emard/ulx3s/doc/esp-wroom-32.jpg

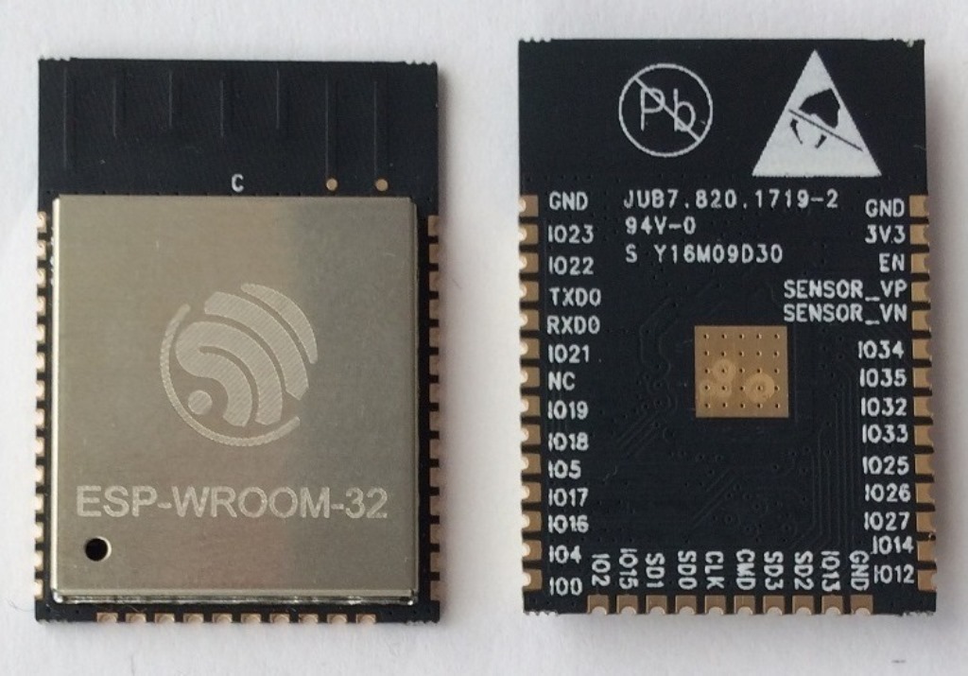
doc/esp-wroom-32.jpg
