emard/ulx3s/doc/oled-ssd1331.jpg

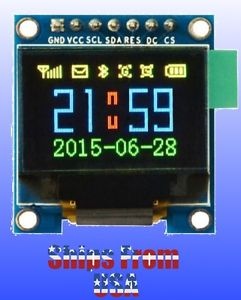
doc/oled-ssd1331.jpg
