emard/ulx3s/doc/sdcard/sdcard-schd3a010/ALPS-SCHD3A0100.GIF

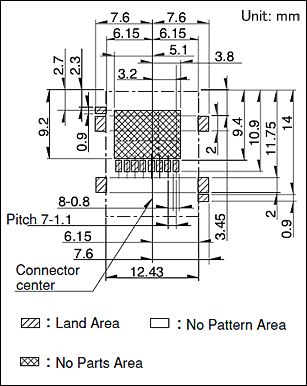
doc/sdcard/sdcard-schd3a010/ALPS-SCHD3A0100.GIF
