emard/ulx3s/pic/ulx3s-v316-bot.jpg

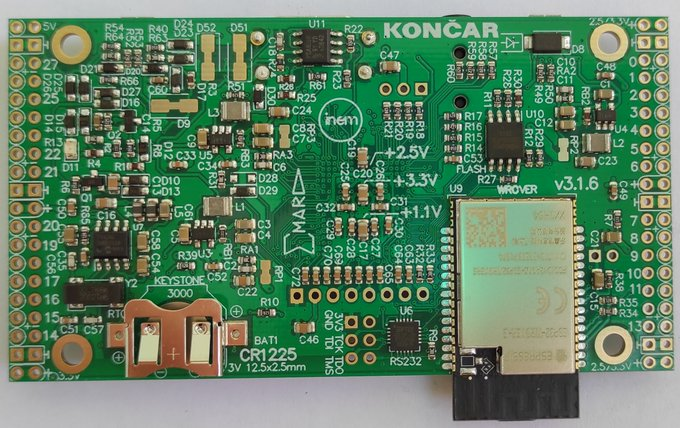
pic/ulx3s-v316-bot.jpg
