emard/ulx3s/pic/ulx3s-v316-top.jpg

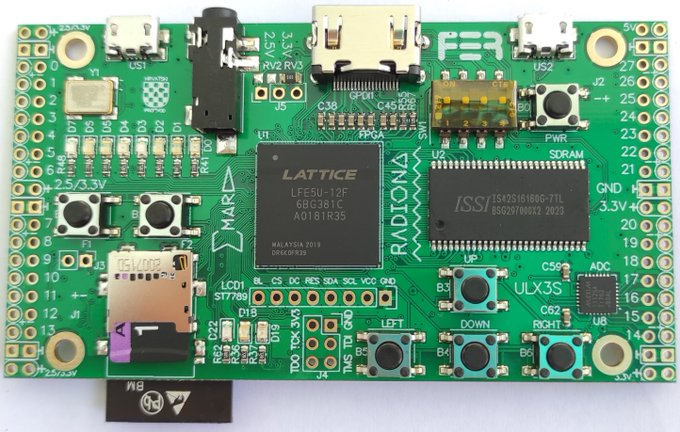
pic/ulx3s-v316-top.jpg
