emard/ulx3s/pic/ULX3S_v303_bottom.png

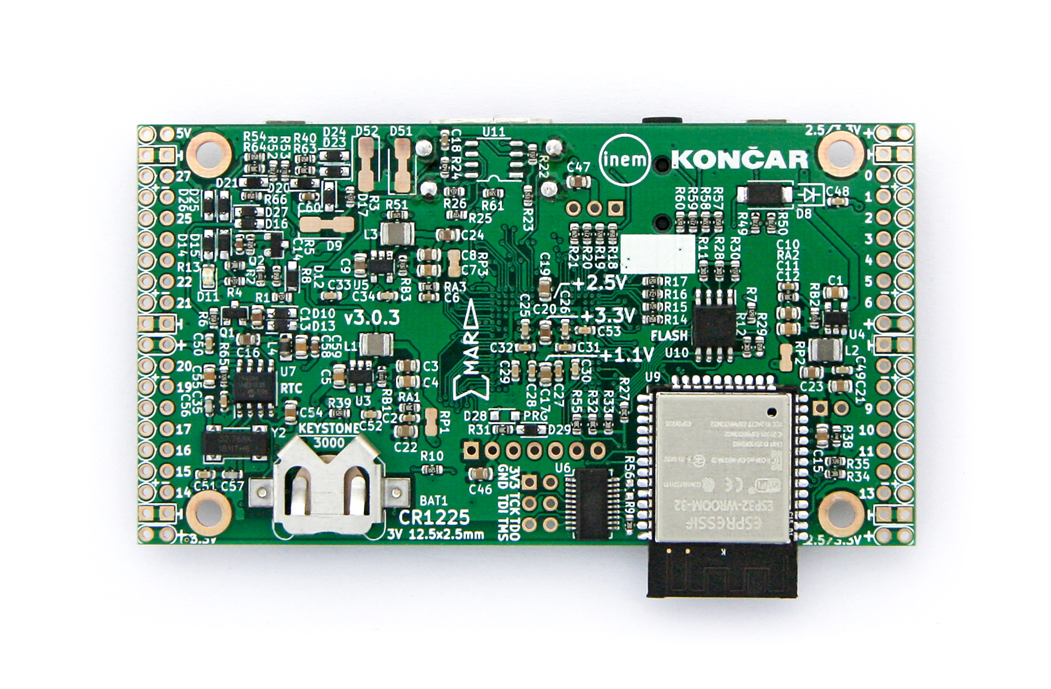
pic/ULX3S_v303_bottom.png
