emard/ulx3s/pic/ULX3S_v303_top.png

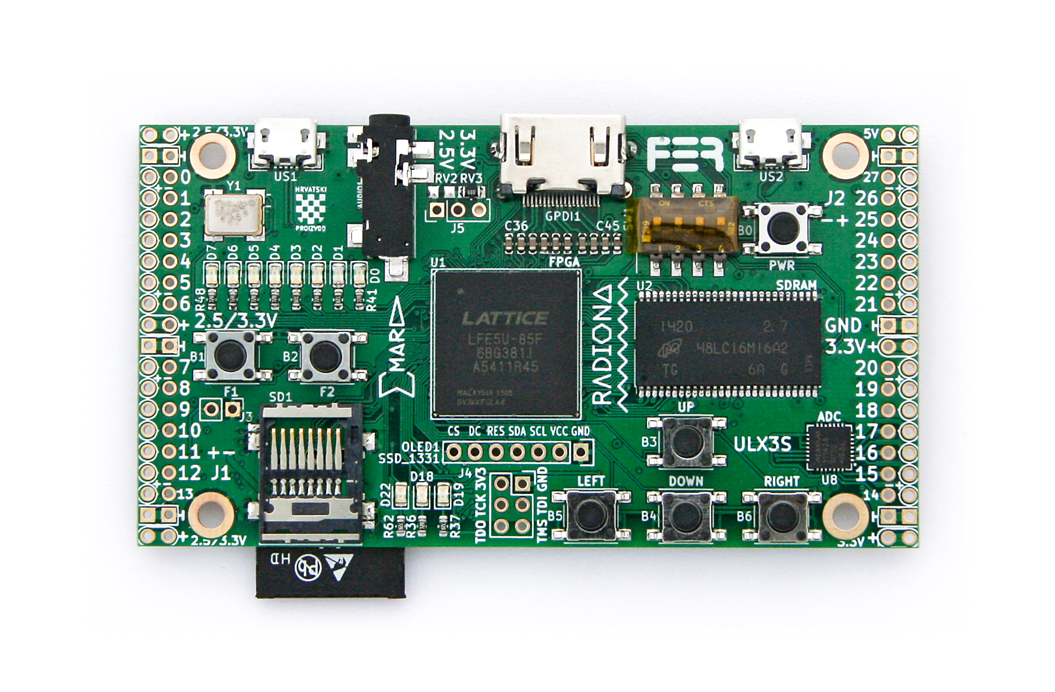
pic/ULX3S_v303_top.png
