emard/ulx3s/pic/ULX3S_v303_XRay1.jpg

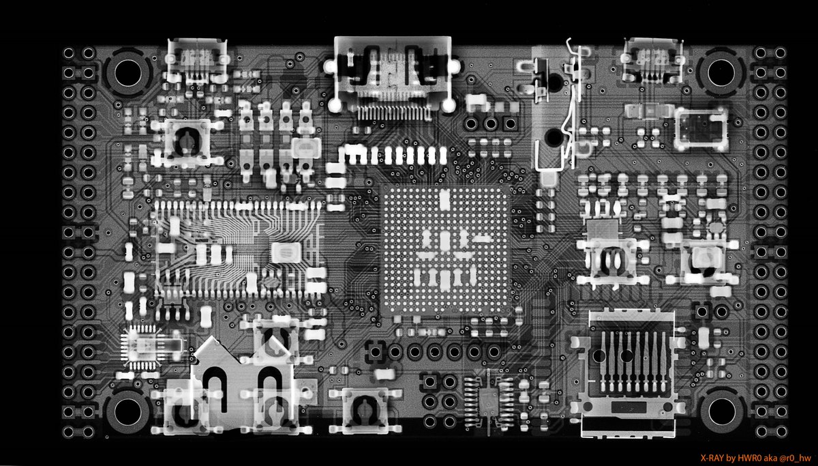
pic/ULX3S_v303_XRay1.jpg
