emard/ulx3s/pic/ULX3S_v303_XRay2.jpg

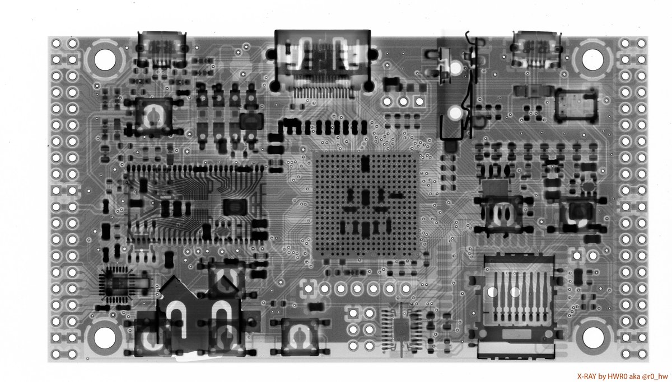
pic/ULX3S_v303_XRay2.jpg
