emard/ulx3s/pic/ULX3S_v303_XRay3.jpg

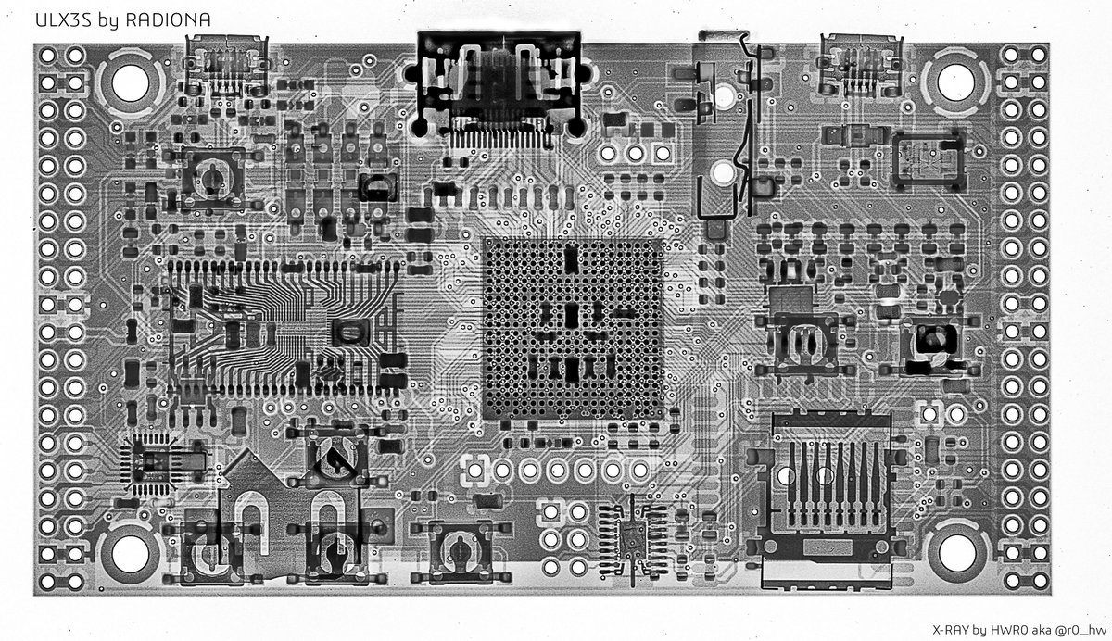
pic/ULX3S_v303_XRay3.jpg
