emard/ulx3s/pic/ULX3S_v307_IR_bottom.jpg

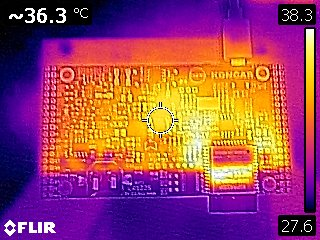
pic/ULX3S_v307_IR_bottom.jpg
