emard/ulx3s/pic/ulx3sb-v17.jpg

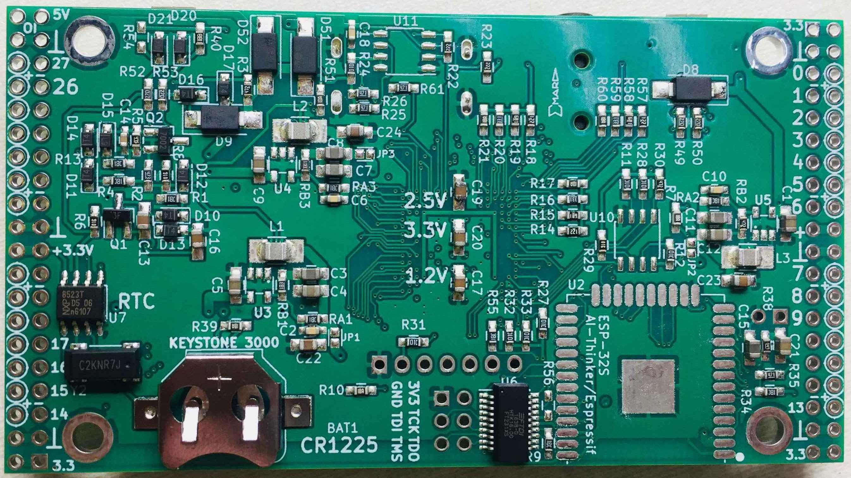
pic/ulx3sb-v17.jpg
