emard/ulx3s/pic/ulx3sb-v18-breakout-c19.png

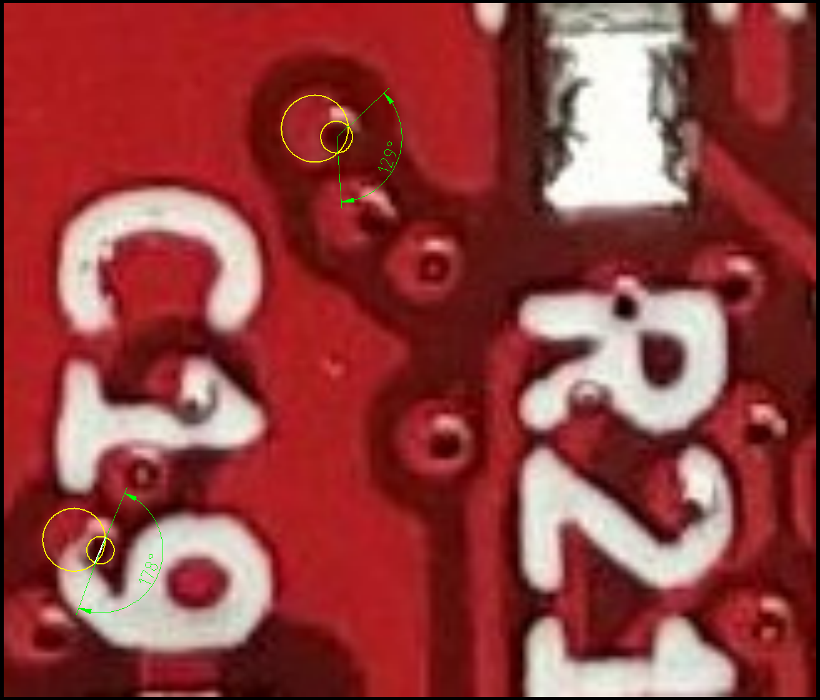
pic/ulx3sb-v18-breakout-c19.png
