emard/ulx3s/pic/ulx3sb-v18.jpg

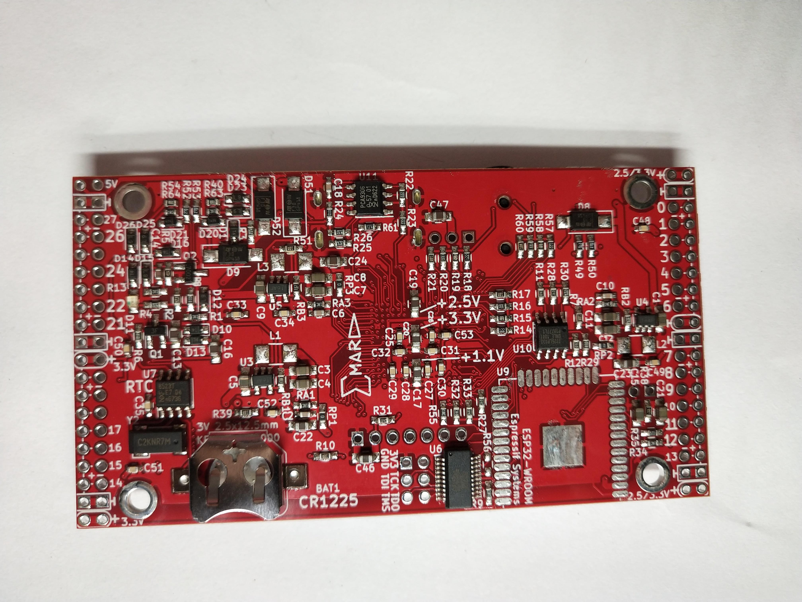
pic/ulx3sb-v18.jpg
