emard/ulx3s/pic/ulx3sb-v212.jpg

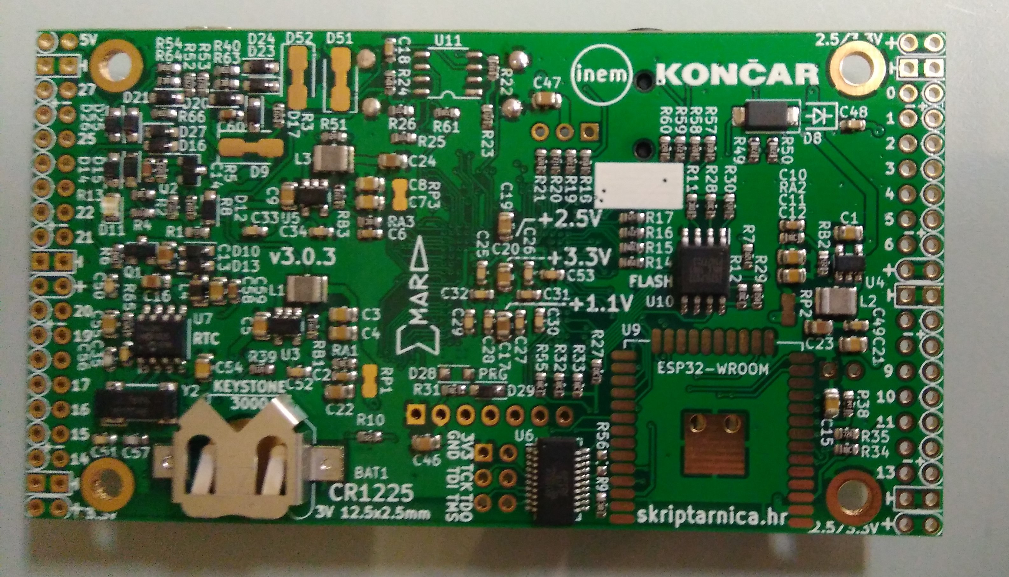
pic/ulx3sb-v212.jpg
