emard/ulx3s/pic/ulx3st-v17.jpg

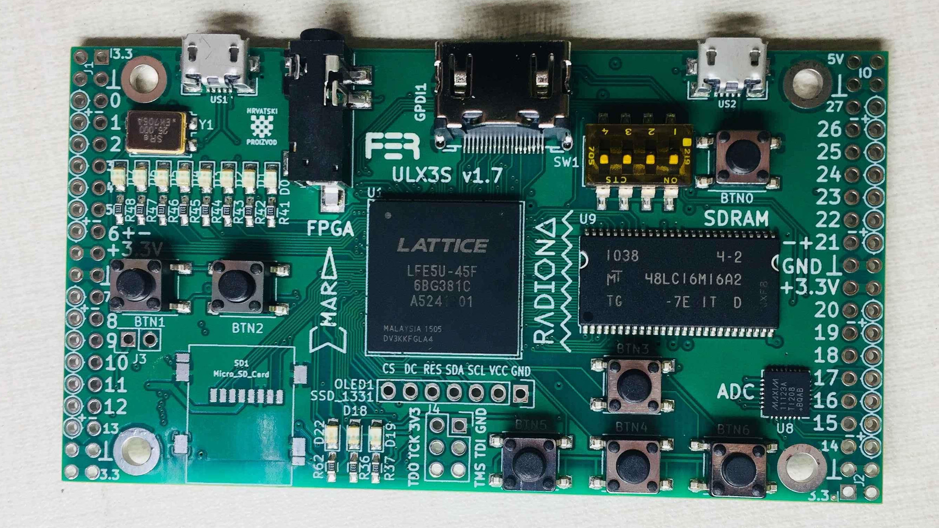
pic/ulx3st-v17.jpg
