emard/ulx3s/pic/ulx3st-v18.jpg

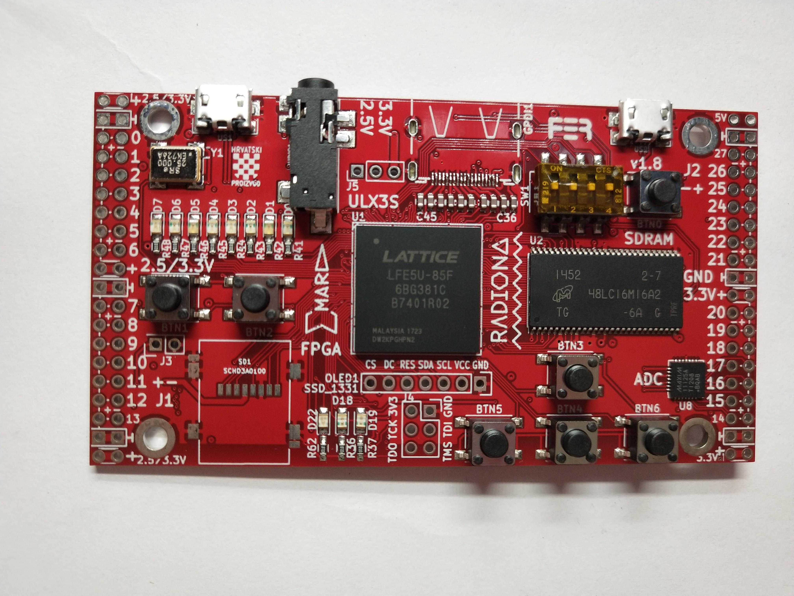
pic/ulx3st-v18.jpg
