emard/ulx3s/pic/ulx3st-v212.jpg

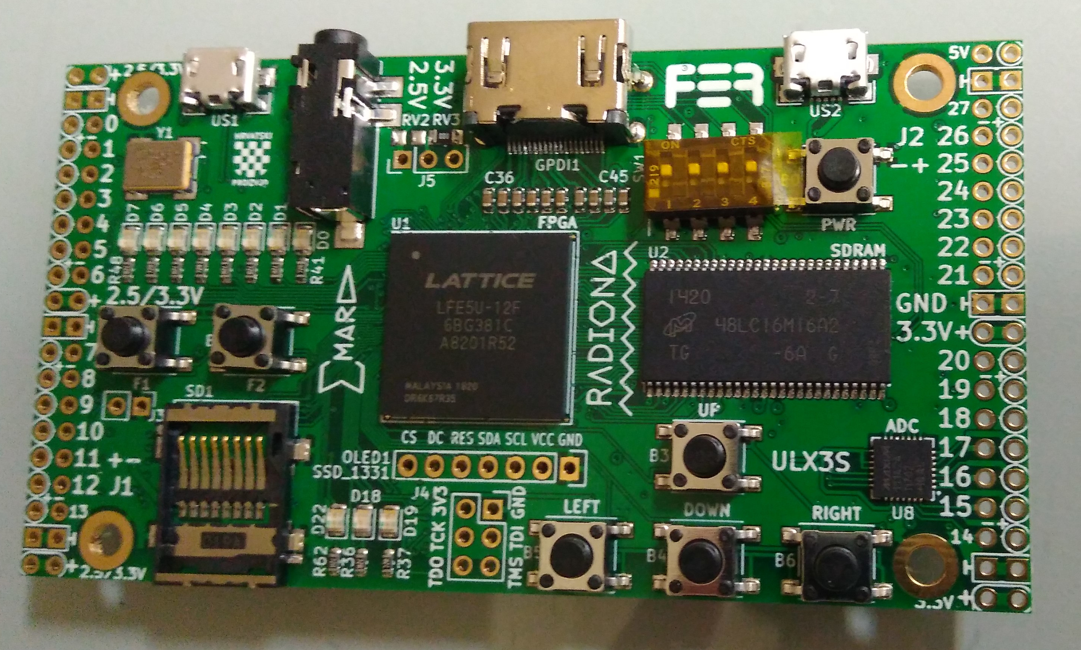
pic/ulx3st-v212.jpg
