emard/ulx3s/pic/ulx3st-v303.jpg

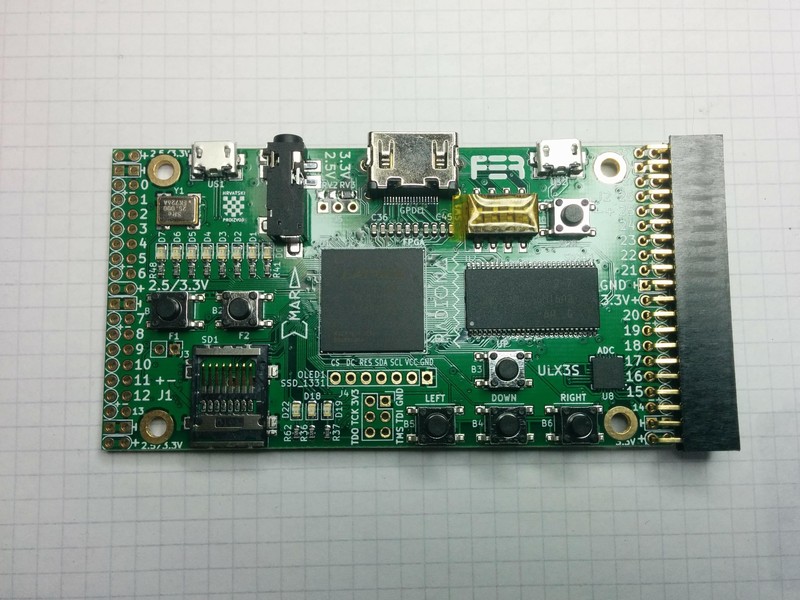
pic/ulx3st-v303.jpg
