emard/ulx3s/doc/schematics_v314.pdf

click on mouse pointer arrow on top of right toolbar
and double-click on sheet to open
Root sheet Sheet: power

Sheet: usb File: usb.sch

Sheet: serdes File: serdes.sch Sheet: flash File: flash.sch Sheet: analog

1 H4 HOLE GND GND GND GND

File: ram.sch Sheet: wifi File: wifi.sch Sheet: gpdi

File: ulx3s.sch Sheet: / EMARD

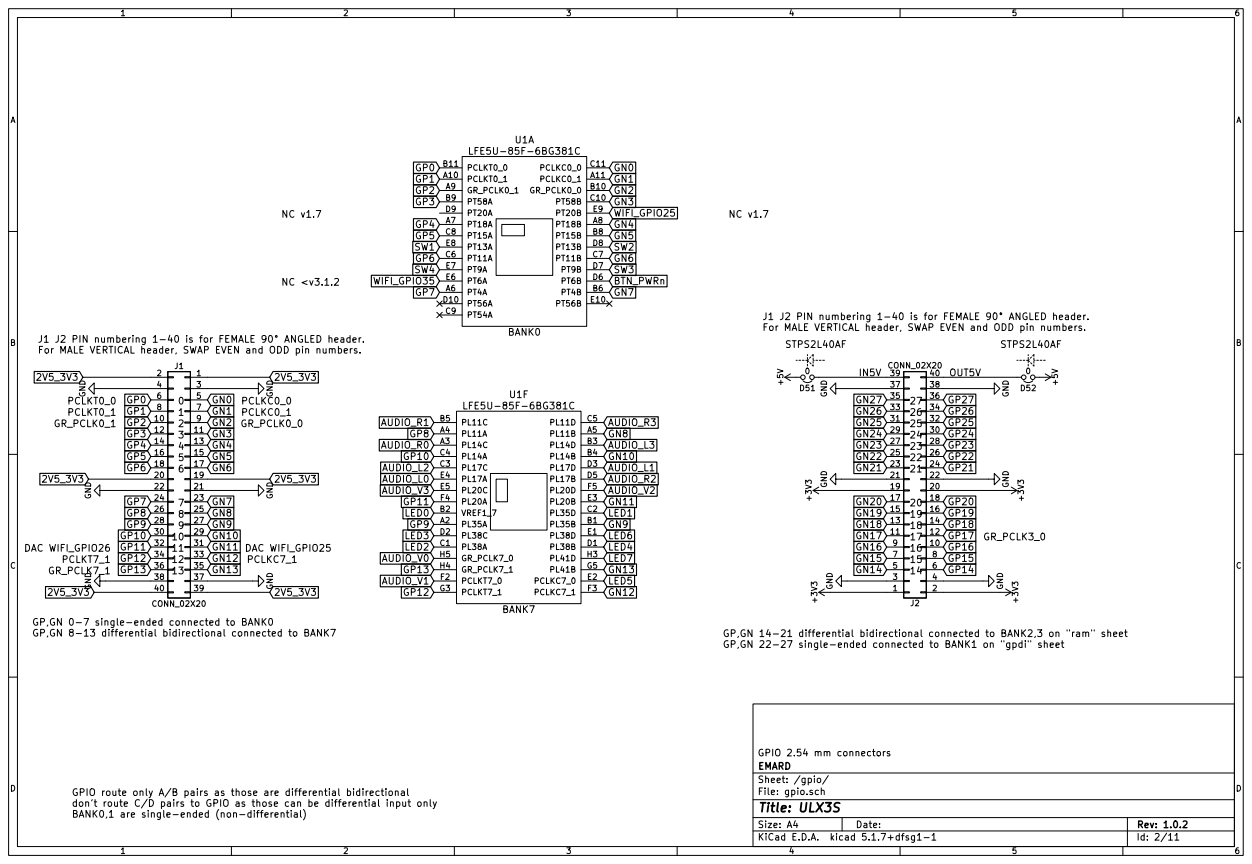
[picture p65: page 2]

J1 J2 PIN numbering 1-40 is for FEMALE 90° ANGLED header.
For MALE VERTICAL header, SWAP EVEN and ODD pin numbers.
STPS2L40AF

STPS2L40AF J1 J2 PIN numbering 1-40 is for FEMALE 90° ANGLED header.

GP,GN 0-7 single-ended connected to BANK0
GP,GN 8-13 differential bidirectional connected to BANK7

GP,GN 22-27 single-ended connected to BANK1 on "gpdi" sheet

GPIO route only A/B pairs as those are differential bidirectional
don't route C/D pairs to GPIO as those can be differential input only

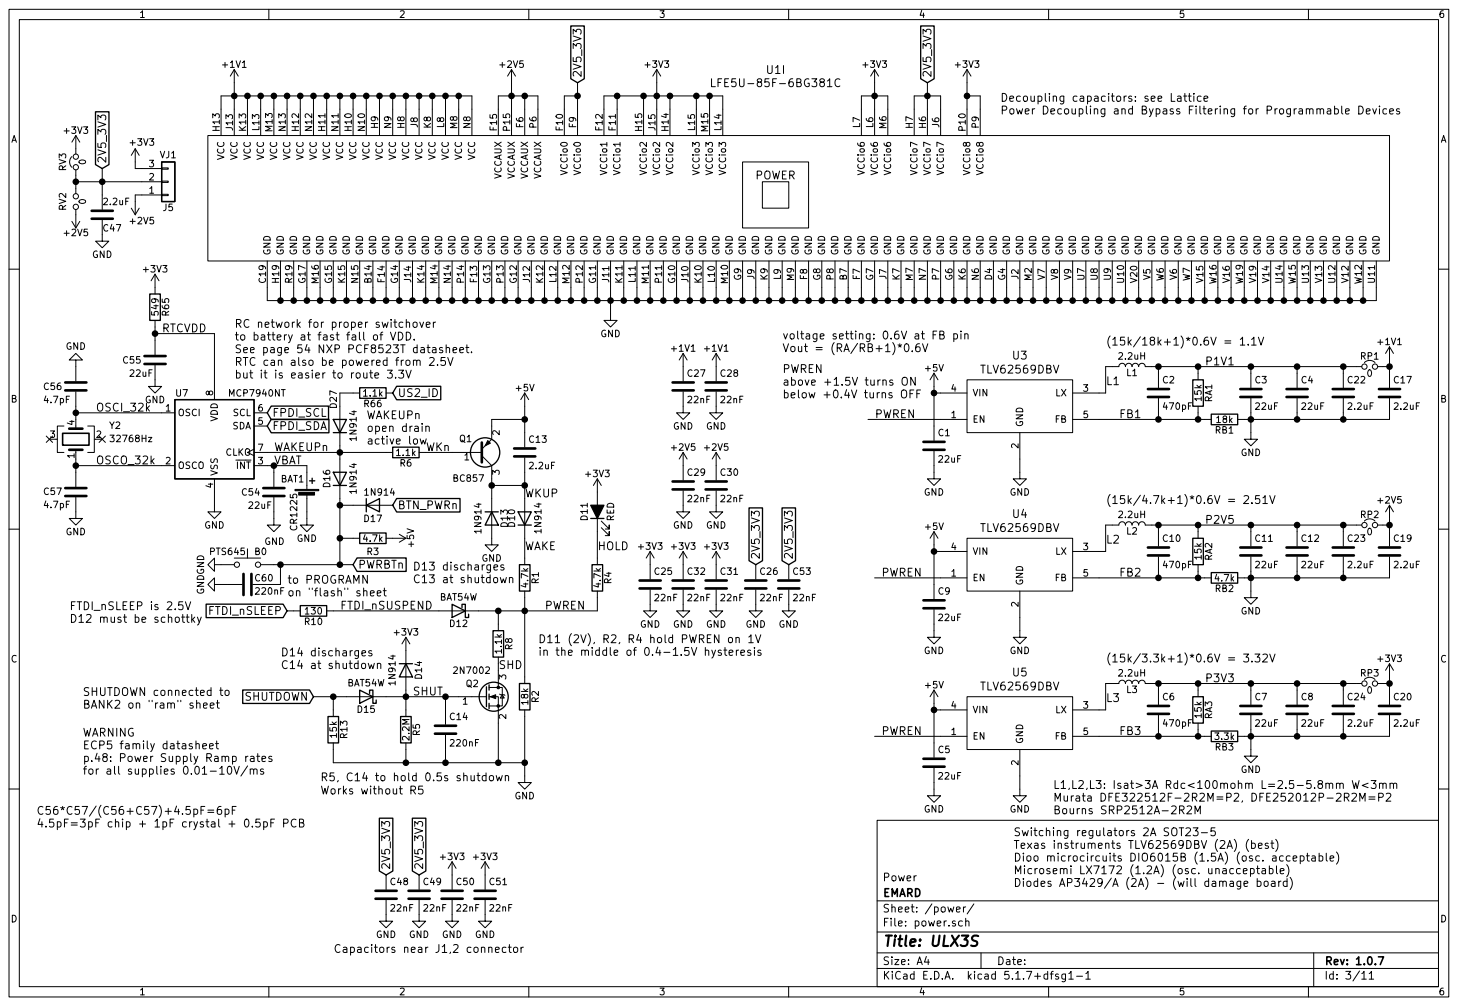
[picture p66: page 3]

RC network for proper switchover
to battery at fast fall of VDD.
See page 54 NXP PCF8523T datasheet.
RTC can also be powered from 2.5V

voltage setting: 0.6V at FB pin
Vout = (RA/RB+1)*0.6V
PWREN
above +1.5V turns ON
below +0.4V turns OFF

4 SDA 5 SCL 6 CLKO 7 VDD
18k BAT1CR1225 GND

open drain active low

D11 (2V), R2, R4 hold PWREN on 1V
in the middle of 0.4-1.5V hysteresis

WARNING
ECP5 family datasheet
p.48: Power Supply Ramp rates
for all supplies 0.01-10V/ms

Switching regulators 2A SOT23-5
Texas instruments TLV62569DBV (2A) (best)
Dioo microcircuits DIO6015B (1.5A) (osc. acceptable)
Microsemi LX7172 (1.2A) (osc. unacceptable)
Diodes AP3429/A (2A) - (will damage board)

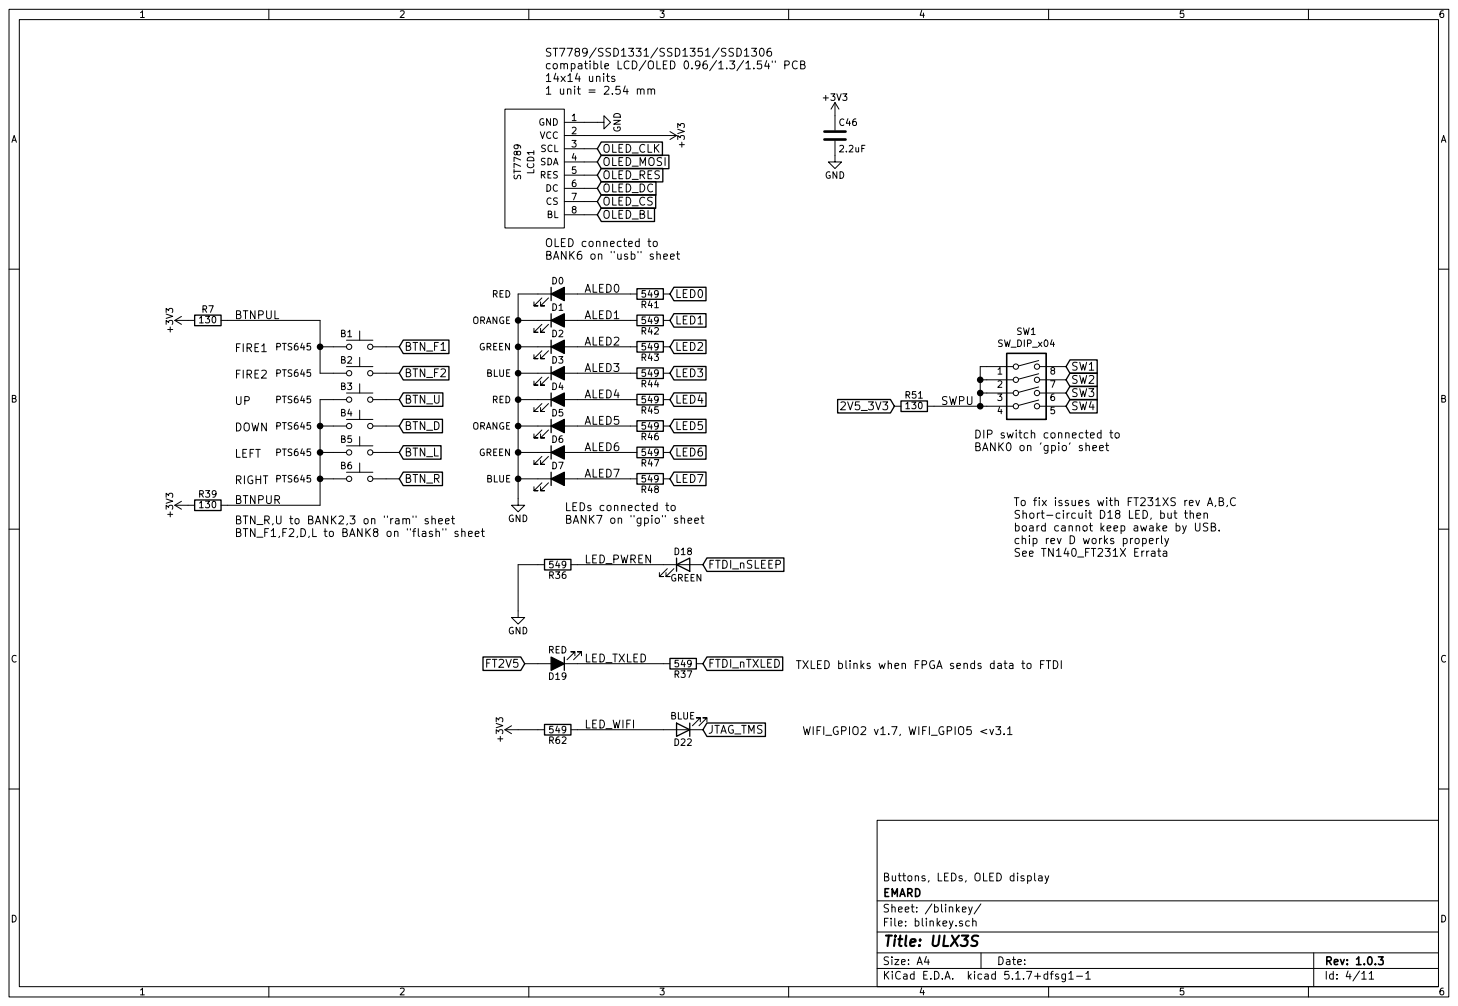
[picture p67: page 4]

ST7789/SSD1331/SSD1351/SSD1306
compatible LCD/OLED 0.96/1.3/1.54" PCB 14x14 units 1 unit = 2.54 mm
D2 GREEN
549 D6 GREEN

OLED connected to BANK6 on "usb" sheet BTN_R,U to BANK2,3 on "ram" sheet

BTN_F1,F2,D,L to BANK8 on "flash" sheet LEFT

LEDs connected to BANK7 on "gpio" sheet

To fix issues with FT231XS rev A,B,C
Short-circuit D18 LED, but then
board cannot keep awake by USB.
chip rev D works properly
See TN140_FT231X Errata

TXLED blinks when FPGA sends data to FTDI

Buttons, LEDs, OLED display
Sheet: /blinkey/ EMARD

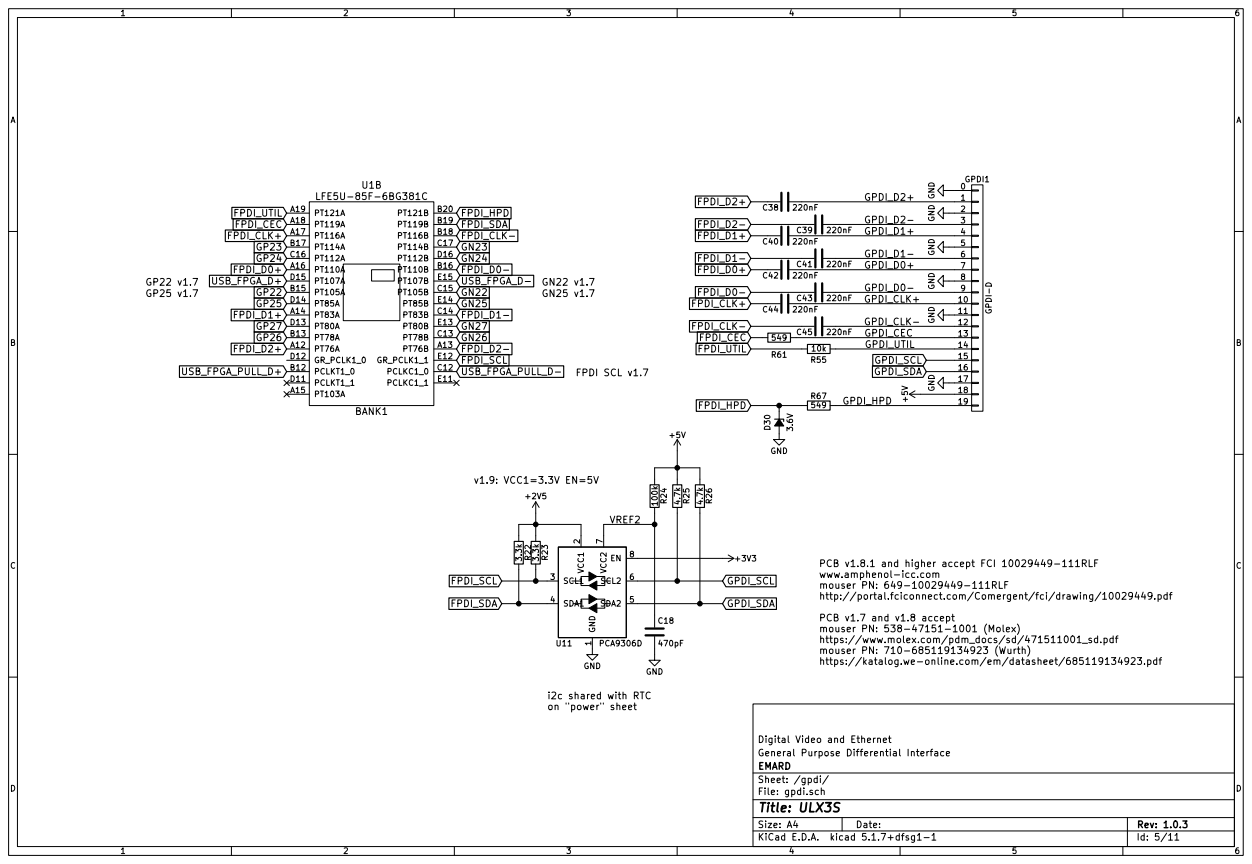
[picture p68: page 5]

FPDI_D2+
Digital Video and Ethernet R61

GPDI_D0+ | 7

GPDI_CLK+ | 10

13
14

PCB v1.8.1 and higher accept FCI 10029449-111RLF
www.amphenol-icc.com
mouser PN: 649-10029449-111RLF
http://portal.fciconnect.com/Comergent/fci/drawing/10029449.pdf

PCB v1.7 and v1.8 accept
mouser PN: 538-47151-1001 (Molex)
https://www.molex.com/pdm_docs/sd/471511001_sd.pdf
mouser PN: 710-685119134923 (Wurth)
https://katalog.we-online.com/em/datasheet/685119134923.pdf

Sheet: /gpdi/ EMARD General Purpose Differential Interface

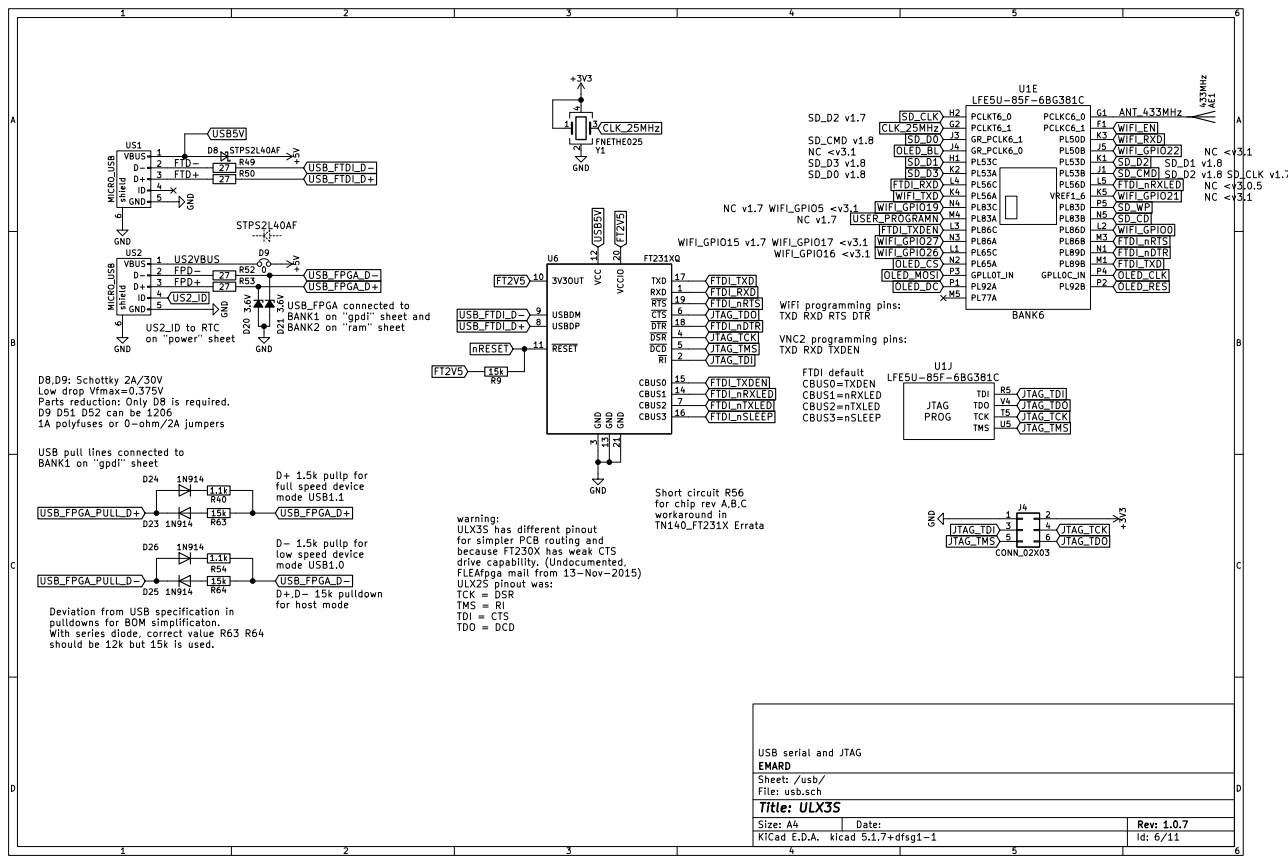
[picture p69: page 6]

3 DSR 4 DCD 5 CTS 6 CBUS2 7 USBDP 8 USBDM 9

WiFi programming pins:
TXD RXD RTS DTR

VNC2 programming pins: TXD RXD TXDEN

D8,D9: Schottky 2A/30V
Low drop Vfmax=0.375V
Parts reduction: Only D8 is required. D9 D51 D52 can be 1206

1A polyfuses or 0-ohm/2A jumpers

USB pull lines connected to
BANK1 on "gpdi" sheet

warning:
ULX3S has different pinout
for simpler PCB routing and
because FT230X has weak CTS
drive capability. (Undocumented,
FLEAfpga mail from 13-Nov-2015)
ULX2S pinout was:
TCK = DSR
TMS = RI
TDI = CTS
TDO = DCD

Deviation from USB specification in
pulldowns for BOM simplificaton.

File: usb.sch Sheet: /usb/ EMARD

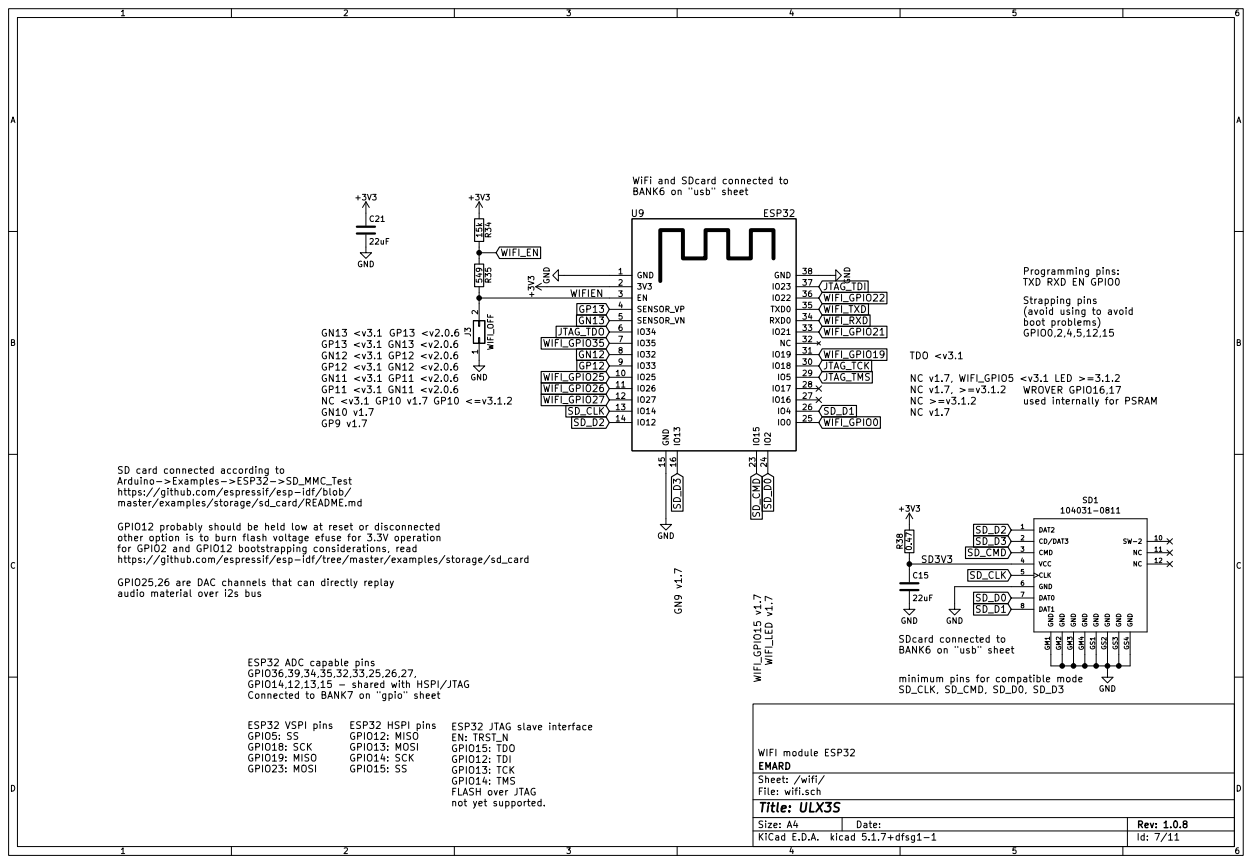
[picture p70: page 7]

WiFi and SDcard connected to BANK6 on "usb" sheet NC <v3.1 GP10 v1.7 GP10 <=v3.1.2

Programming pins:
TXD RXD EN GPIO0
Strapping pins
(avoid using to avoid
boot problems)
GPIO0,2,4,5,12,15
SDcard connected to BANK6 on "usb" sheet NC v1.7

WROVER GPIO16,17
used internally for PSRAM

GPIO25,26 are DAC channels that can directly replay audio material over i2s bus SD card connected according to
Arduino->Examples->ESP32->SD_MMC_Test
https://github.com/espressif/esp-idf/blob/
master/examples/storage/sd_card/README.md

GPIO12 probably should be held low at reset or disconnected
other option is to burn flash voltage efuse for 3.3V operation
for GPIO2 and GPIO12 bootstrapping considerations, read
https://github.com/espressif/esp-idf/tree/master/examples/storage/sd_card

ESP32 ADC capable pins
GPIO36,39,34,35,32,33,25,26,27,
GPIO14,12,13,15 - shared with HSPI/JTAG
Connected to BANK7 on "gpio" sheet

File: wifi.sch Sheet: /wifi/ EMARD WIFI module ESP32

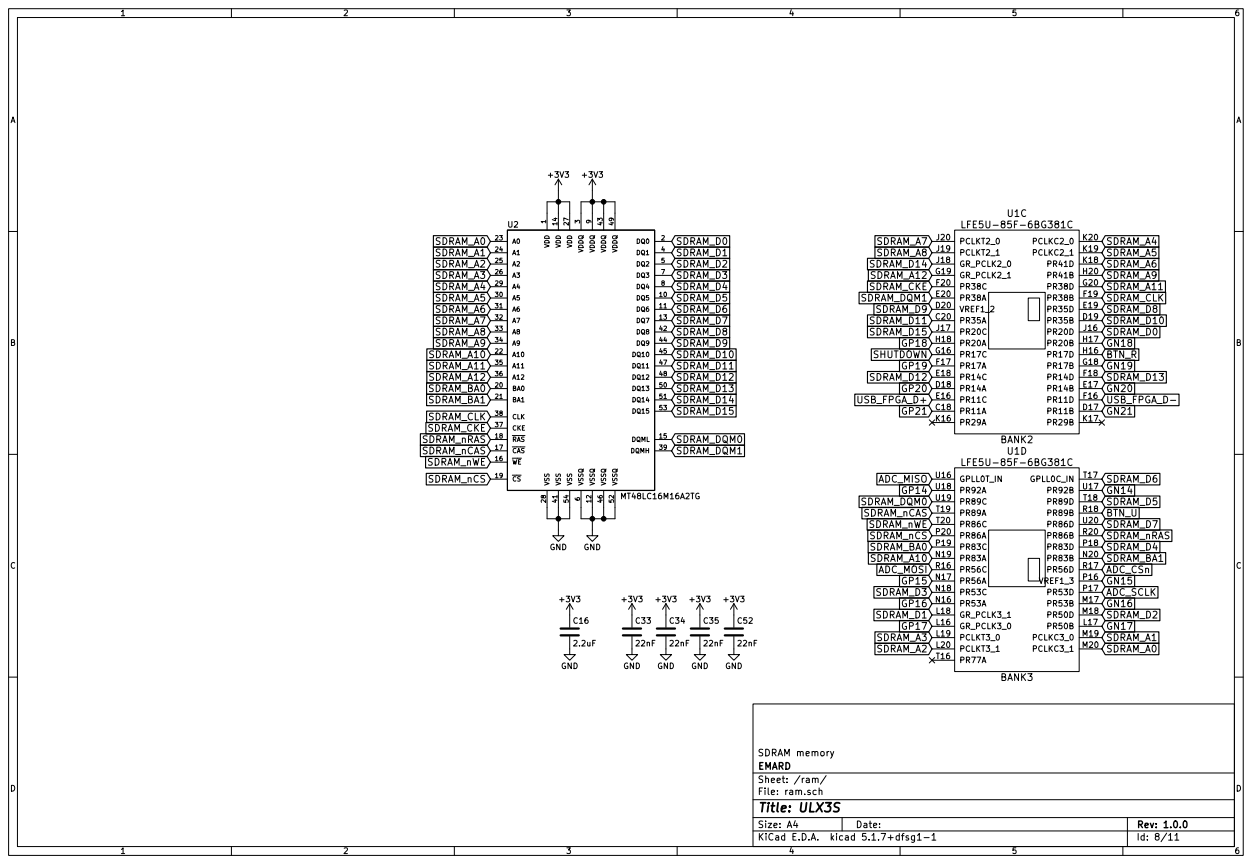
[picture p71: page 8]

File: ram.sch Sheet: /ram/ EMARD

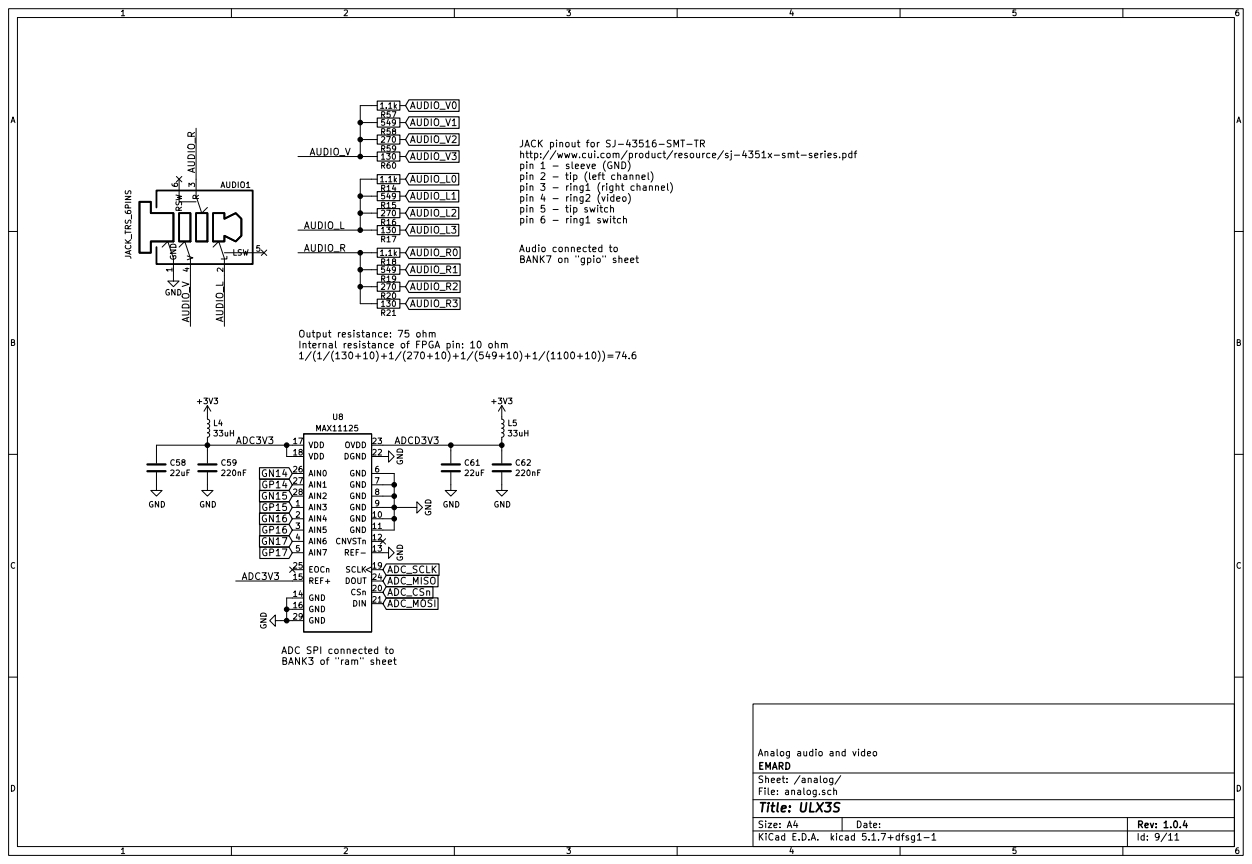
[picture p72: page 9]

JACK pinout for SJ-43516-SMT-TR
http://www.cui.com/product/resource/sj-4351x-smt-series.pdf
pin 1 - sleeve (GND)
pin 2 - tip (left channel)
pin 3 - ring1 (right channel)
pin 4 - ring2 (video)
pin 5 - tip switch
pin 6 - ring1 switch Audio connected to BANK7 on "gpio" sheet

Output resistance: 75 ohm
Internal resistance of FPGA pin: 10 ohm

Analog audio and video GND

ADC SPI connected to BANK3 of "ram" sheet

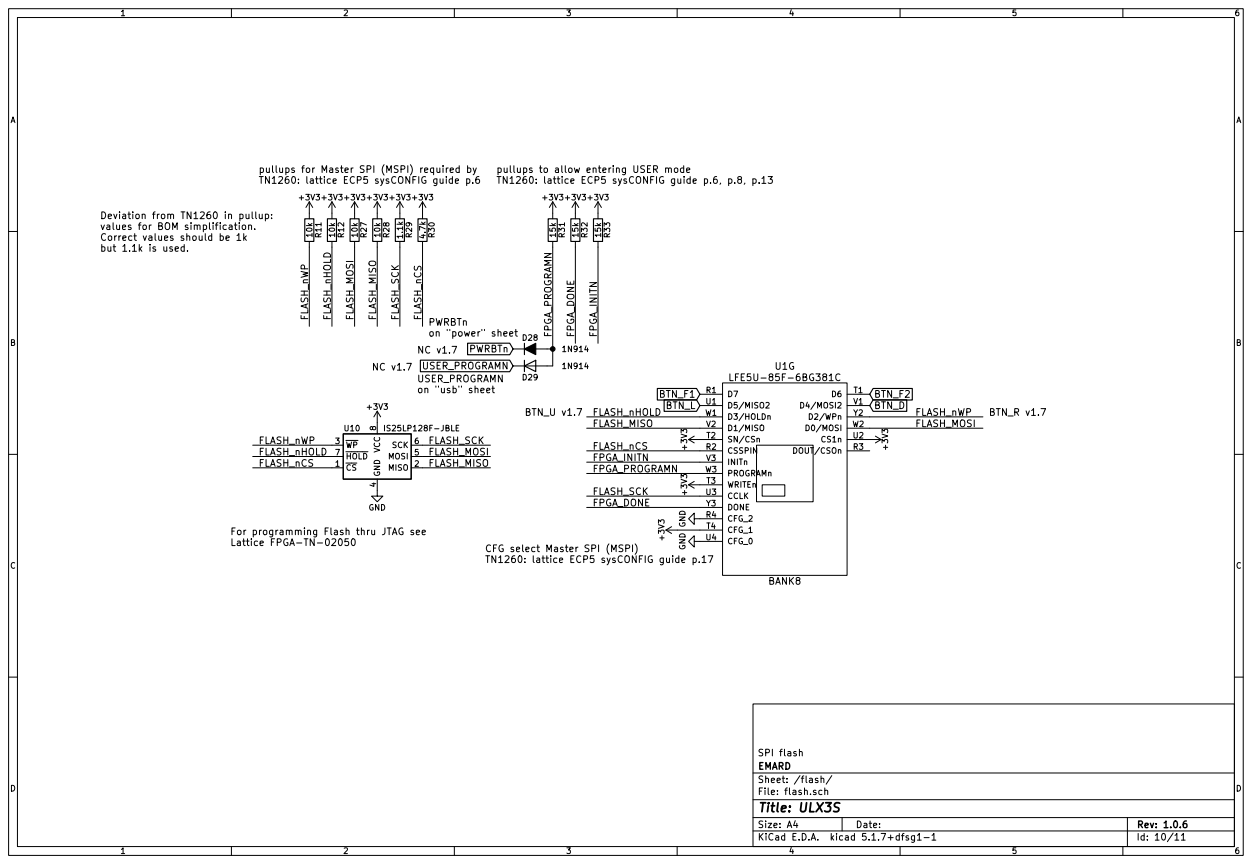
[picture p73: page 10]

pullups for Master SPI (MSPI) required by
TN1260: lattice ECP5 sysCONFIG guide p.6

pullups to allow entering USER mode
TN1260: lattice ECP5 sysCONFIG guide p.6, p.8, p.13

Deviation from TN1260 in pullup:
values for BOM simplification.

FLASH_nHOLD | FLASH_MOSI
FLASH_nCS

4 MOSI 5 SCK 6 HOLD 7 VCC

For programming Flash thru JTAG see
Lattice FPGA-TN-02050

CFG select Master SPI (MSPI)
TN1260: lattice ECP5 sysCONFIG guide p.17

File: flash.sch Sheet: /flash/ EMARD

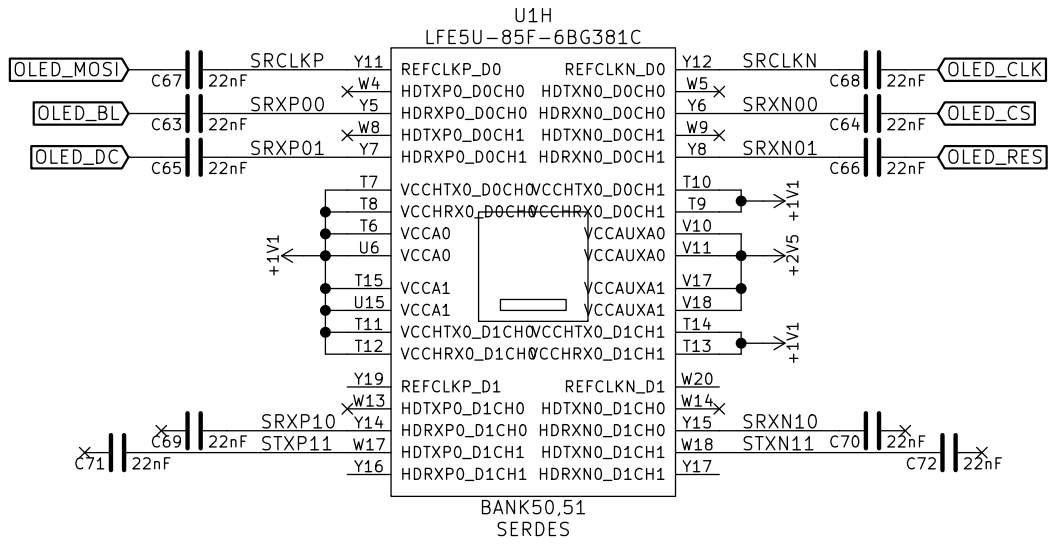
[picture p74: page 11]

File: serdes.sch Sheet: /serdes/ EMARD
