emard/ulx3s/doc/schematics_v308.pdf

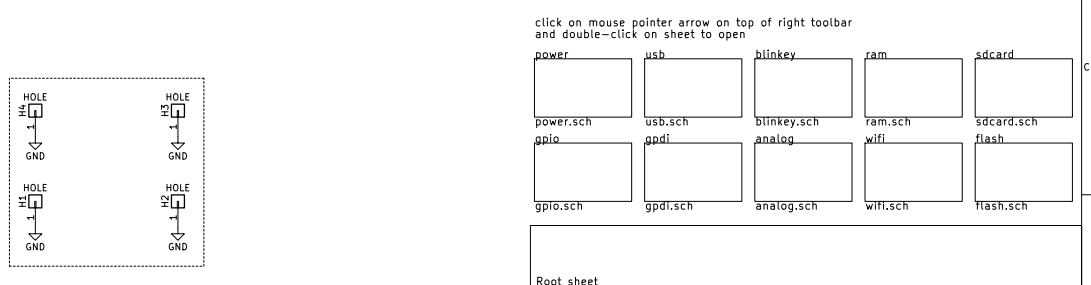
[picture p75: page 1]

click on mouse pointer arrow on top of right toolbar
and double-click on sheet to open
power power.sch
Root sheet gpio

1 H4 HOLE GND GND GND GND

File: ulx3s.sch Sheet: / EMARD

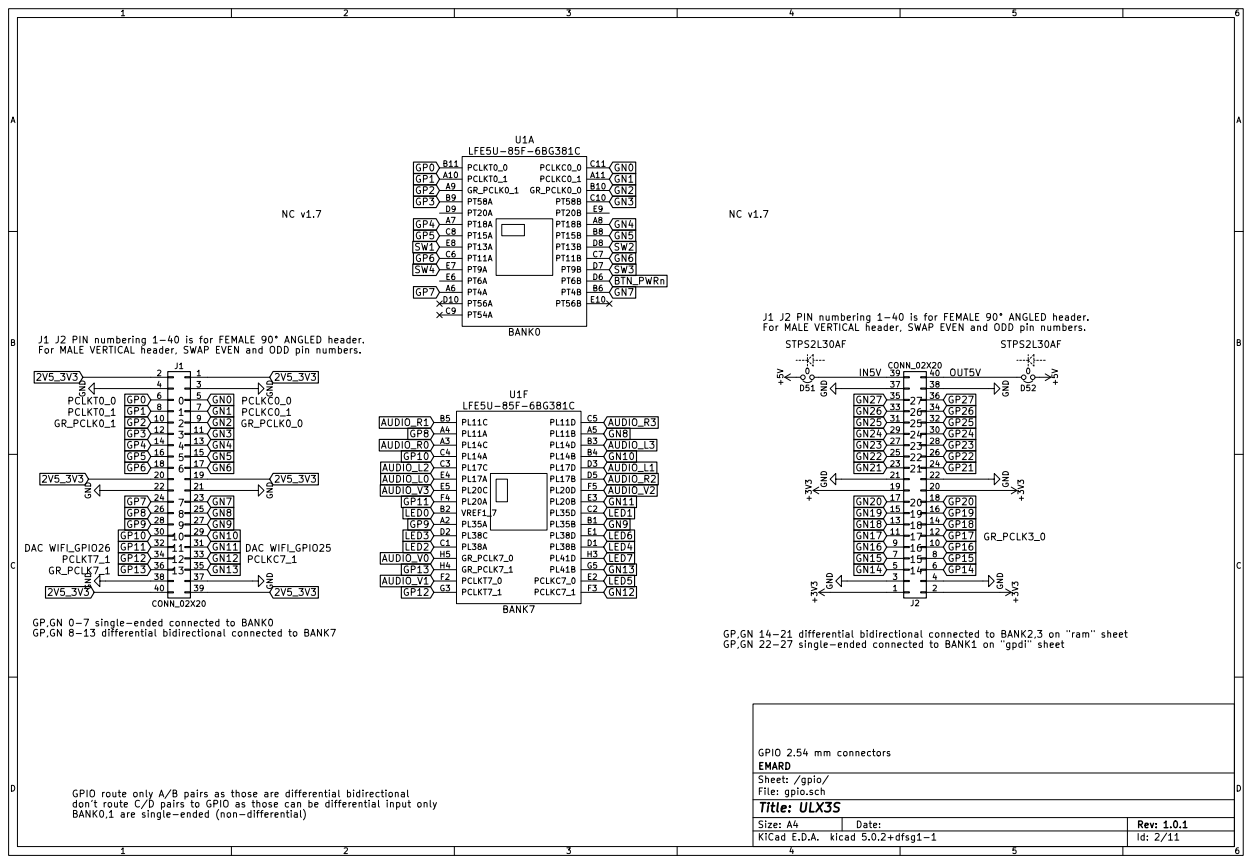
[picture p76: page 2]

J1 J2 PIN numbering 1-40 is for FEMALE 90° ANGLED header.
For MALE VERTICAL header, SWAP EVEN and ODD pin numbers.

LED7 GPIO route only A/B pairs as those are differential bidirectional
GR_PCLK7_1

GP,GN 0-7 single-ended connected to BANK0
GP,GN 8-13 differential bidirectional connected to BANK7

GP,GN 14-21 differential bidirectional connected to BANK2,3 on "ram" sheet
GP,GN 22-27 single-ended connected to BANK1 on "gpdi" sheet

don't route C/D pairs to GPIO as those can be differential input only
BANK0,1 are single-ended (non-differential)

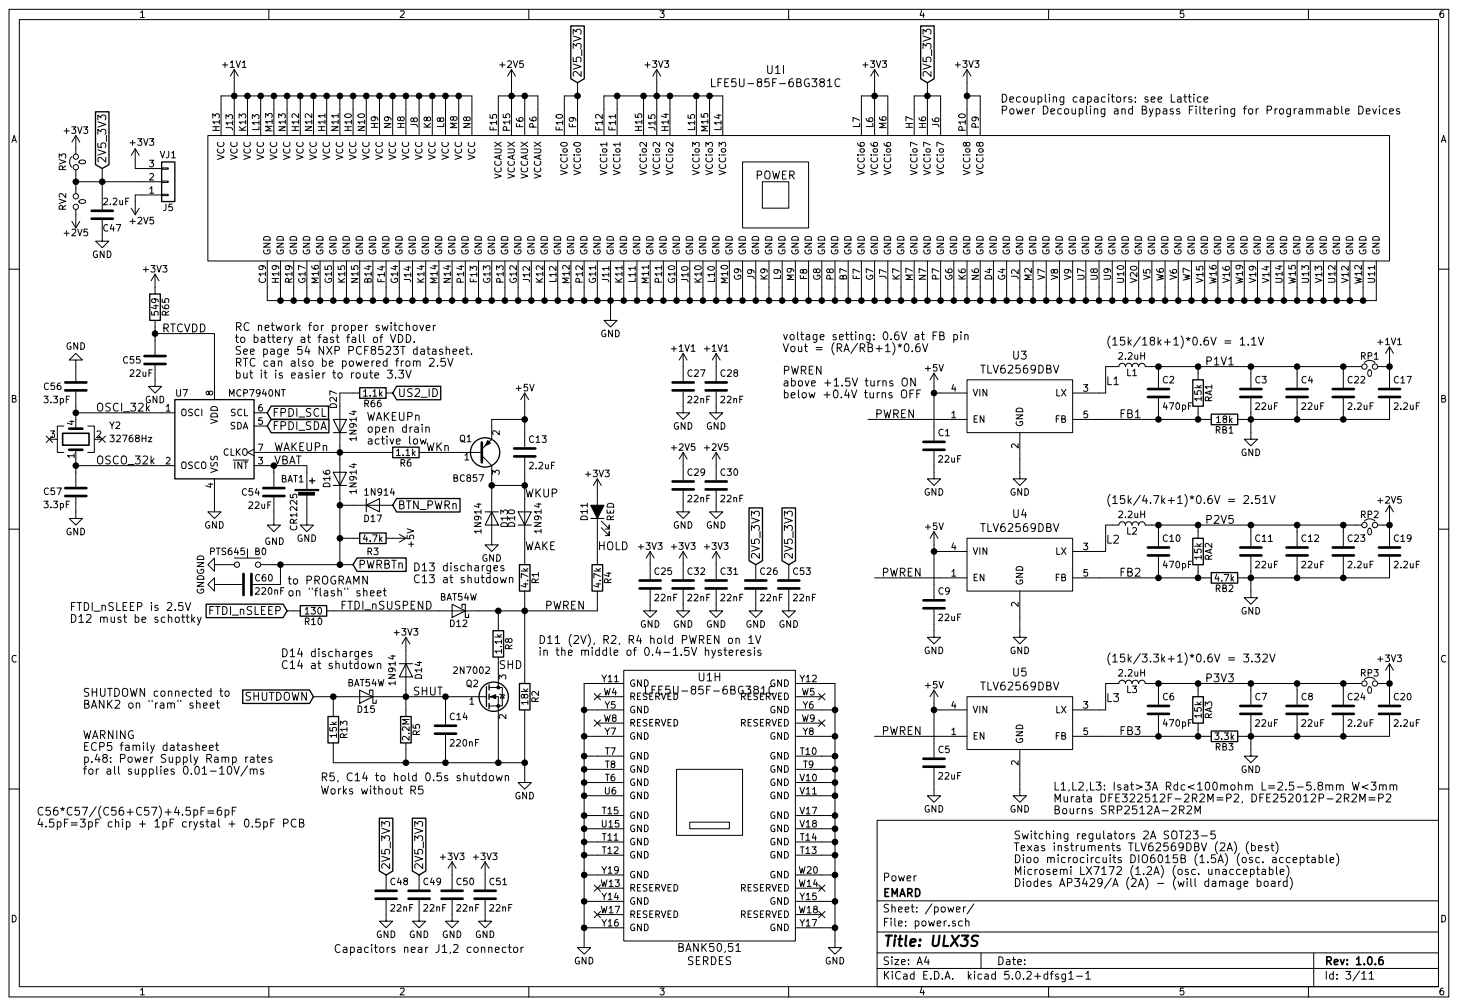
[picture p77: page 3]

Power Decoupling and Bypass Filtering for Programmable Devices C25

+3V3 voltage setting: 0.6V at FB pin
Vout = (RA/RB+1)*0.6V

to battery at fast fall of VDD.
See page 54 NXP PCF8523T datasheet.
RTC can also be powered from 2.5V
but it is easier to route 3.3V

4 SDA 5 SCL 6 CLKO 7 VDD

D11 (2V), R2, R4 hold PWREN on 1V
in the middle of 0.4-1.5V hysteresis

WARNING
ECP5 family datasheet
p.48: Power Supply Ramp rates
for all supplies 0.01-10V/ms

Texas instruments TLV62569DBV (2A) (best)
Dioo microcircuits DIO6015B (1.5A) (osc. acceptable)
Microsemi LX7172 (1.2A) (osc. unacceptable)
Diodes AP3429/A (2A) - (will damage board)

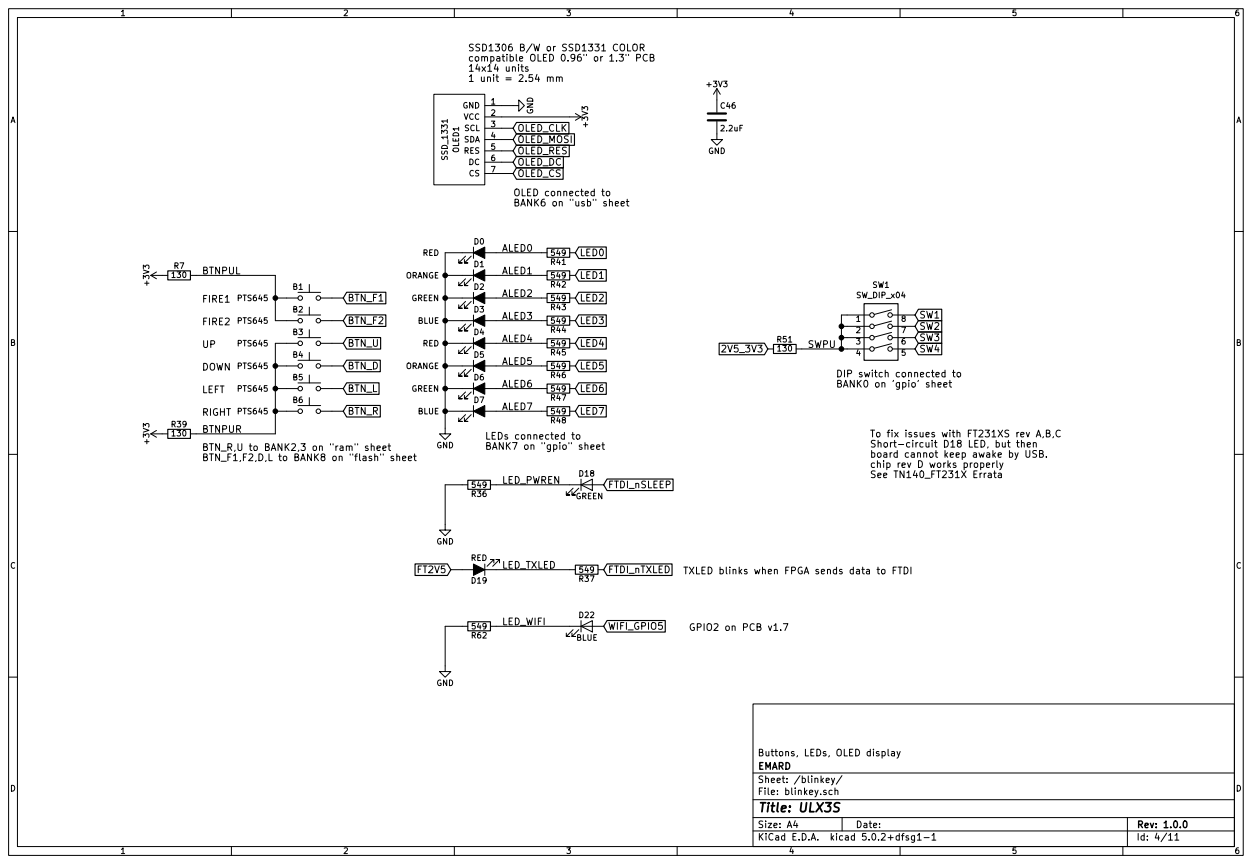
[picture p78: page 4]

compatible OLED 0.96" or 1.3" PCB 14x14 units 1 unit = 2.54 mm

To fix issues with FT231XS rev A,B,C
Short-circuit D18 LED, but then
board cannot keep awake by USB.
chip rev D works properly
See TN140_FT231X Errata

TXLED blinks when FPGA sends data to FTDI

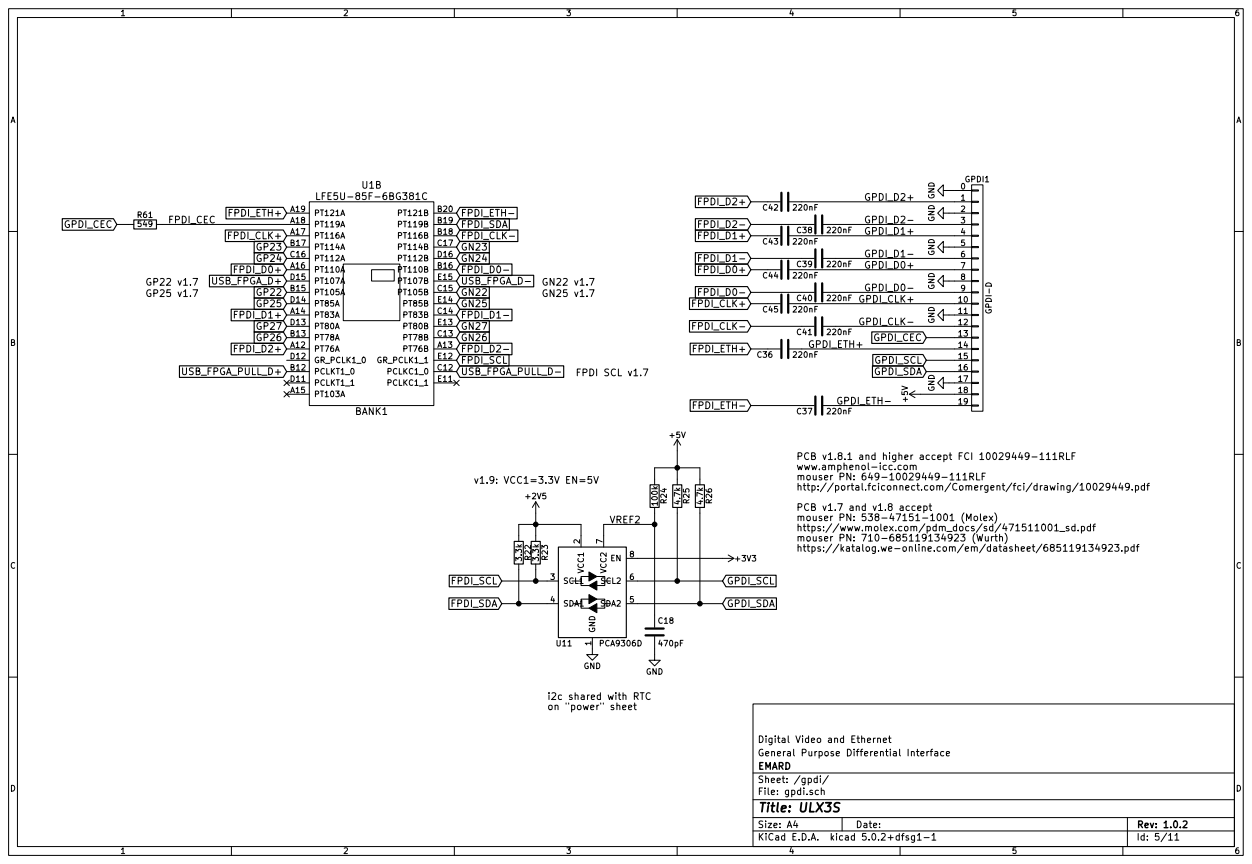
[picture p79: page 5]

9GPDI1 GPDI-D GND GND GND GND GND GND +5V
GPDI_D2+

GPDI_D1+ | 4

GPDI_D0+ | 7

GPDI_CLK+ | 10

PCB v1.8.1 and higher accept FCI 10029449-111RLF
www.amphenol-icc.com
mouser PN: 649-10029449-111RLF
http://portal.fciconnect.com/Comergent/fci/drawing/10029449.pdf
PCB v1.7 and v1.8 accept
mouser PN: 538-47151-1001 (Molex)
https://www.molex.com/pdm_docs/sd/471511001_sd.pdf
mouser PN: 710-685119134923 (Wurth)

7 EN 8 U11 PCA9306D
https://katalog.we-online.com/em/datasheet/685119134923.pdf GND

Digital Video and Ethernet
Sheet: /gpdi/ EMARD General Purpose Differential Interface

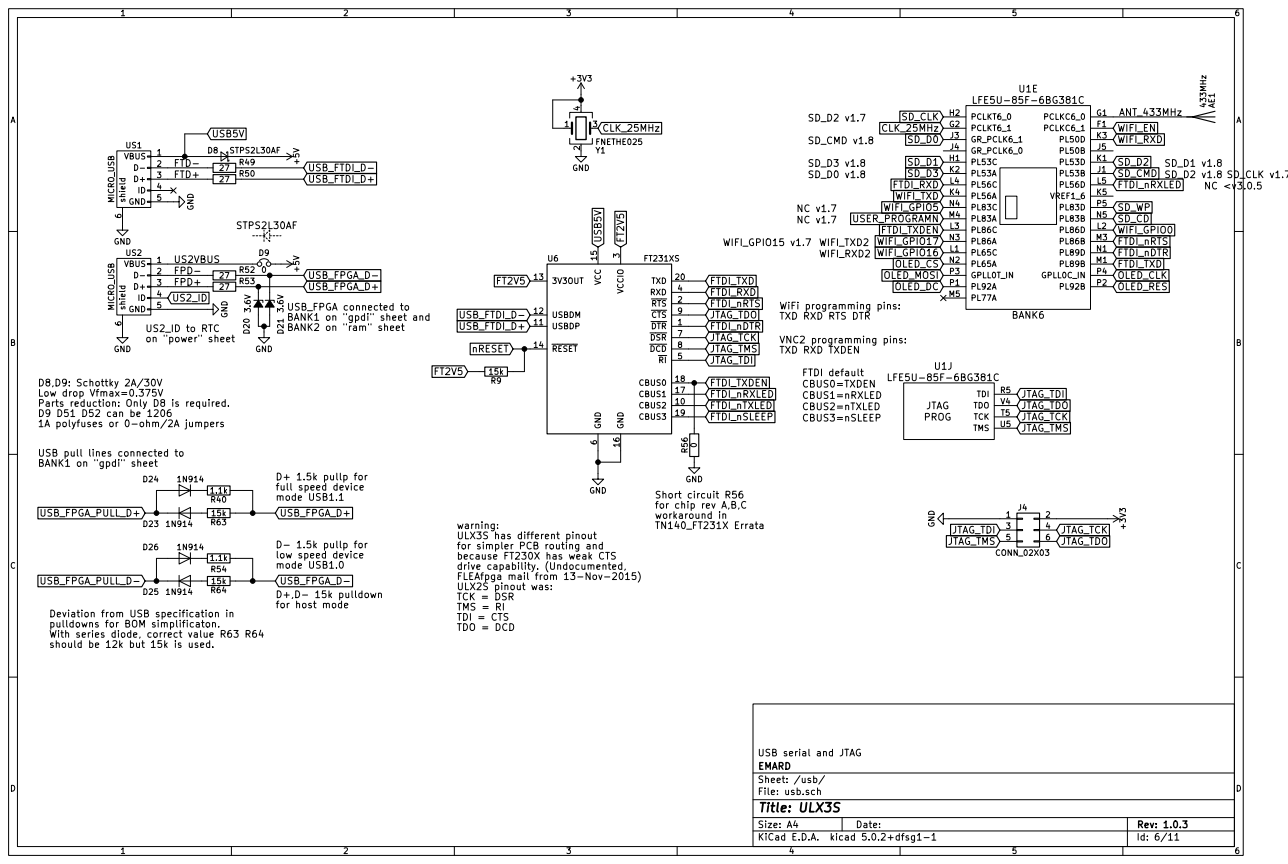
[picture p80: page 6]

BANK1 on "gpdi" sheet and BANK2 on "ram" sheet R52

6 DSR 7 DCD 8 CTS 9 CBUS2 10 TXD 20 USBDP 11 USBDM 12

WiFi programming pins:
TXD RXD RTS DTR

VNC2 programming pins: TXD RXD TXDEN

D8,D9: Schottky 2A/30V
Low drop Vfmax=0.375V
Parts reduction: Only D8 is required. D9 D51 D52 can be 1206

15k USB pull lines connected to

warning:
ULX3S has different pinout
for simpler PCB routing and
because FT230X has weak CTS
drive capability. (Undocumented,
FLEAfpga mail from 13-Nov-2015)
ULX2S pinout was:
TCK = DSR
TMS = RI
TDI = CTS
TDO = DCD

Deviation from USB specification in
pulldowns for BOM simplificaton.

USB serial and JTAG
File: usb.sch Sheet: /usb/ EMARD

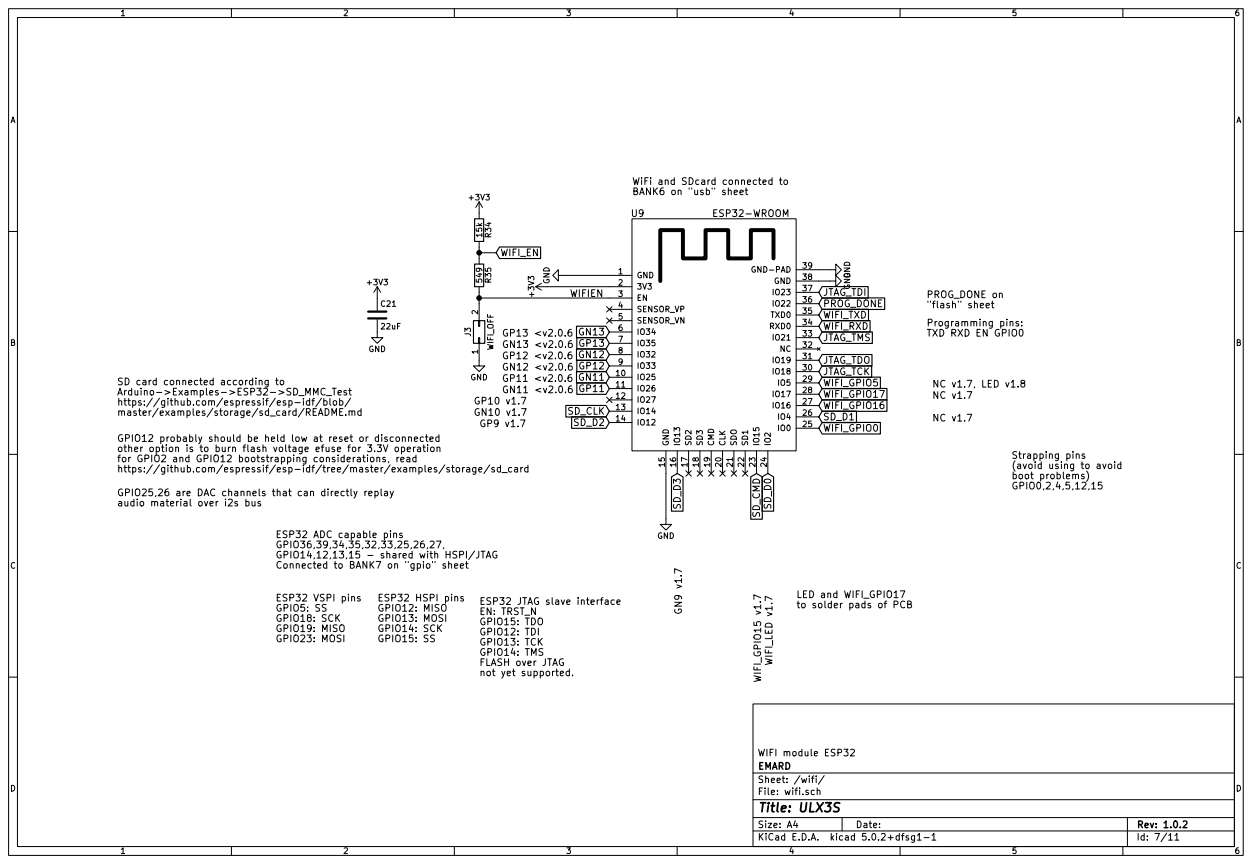
[picture p81: page 7]

GPIO25,26 are DAC channels that can directly replay audio material over i2s bus SD card connected according to
Arduino->Examples->ESP32->SD_MMC_Test
https://github.com/espressif/esp-idf/blob/

other option is to burn flash voltage efuse for 3.3V operation
for GPIO2 and GPIO12 bootstrapping considerations, read
https://github.com/espressif/esp-idf/tree/master/examples/storage/sd_card

(avoid using to avoid
boot problems)
GPIO0,2,4,5,12,15

ESP32 ADC capable pins
GPIO36,39,34,35,32,33,25,26,27,
GPIO14,12,13,15 - shared with HSPI/JTAG
Connected to BANK7 on "gpio" sheet

LED and WIFI_GPIO17
to solder pads of PCB

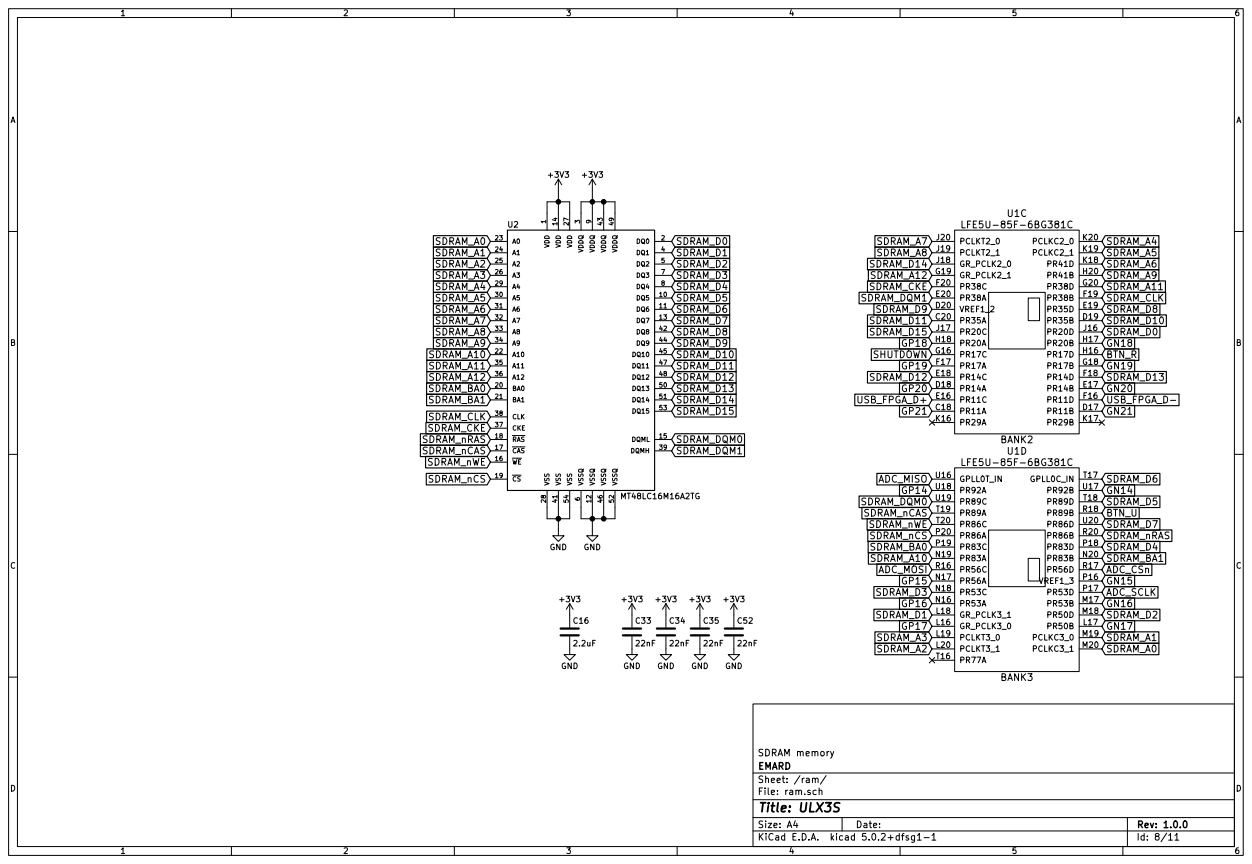
[picture p82: page 8]

SDRAM memory
File: ram.sch Sheet: /ram/ EMARD

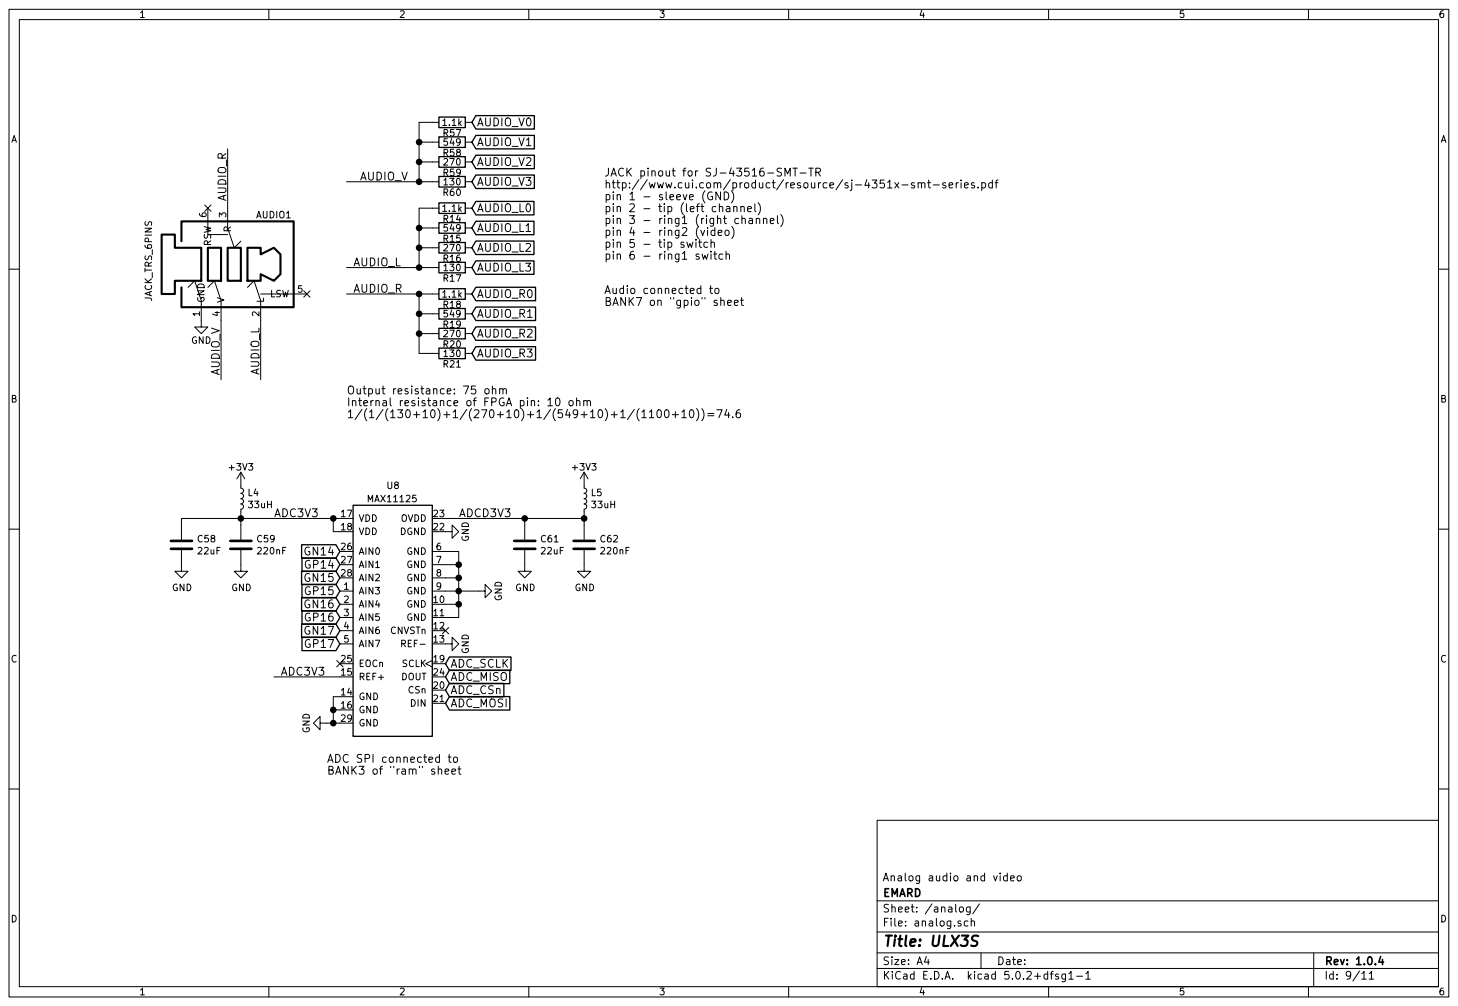
[picture p83: page 9]

JACK pinout for SJ-43516-SMT-TR
http://www.cui.com/product/resource/sj-4351x-smt-series.pdf
pin 1 - sleeve (GND)
pin 2 - tip (left channel)
pin 3 - ring1 (right channel)
pin 4 - ring2 (video)
pin 5 - tip switch

Analog audio and video GND

Internal resistance of FPGA pin: 10 ohm

ADC SPI connected to BANK3 of "ram" sheet ADC_MISO

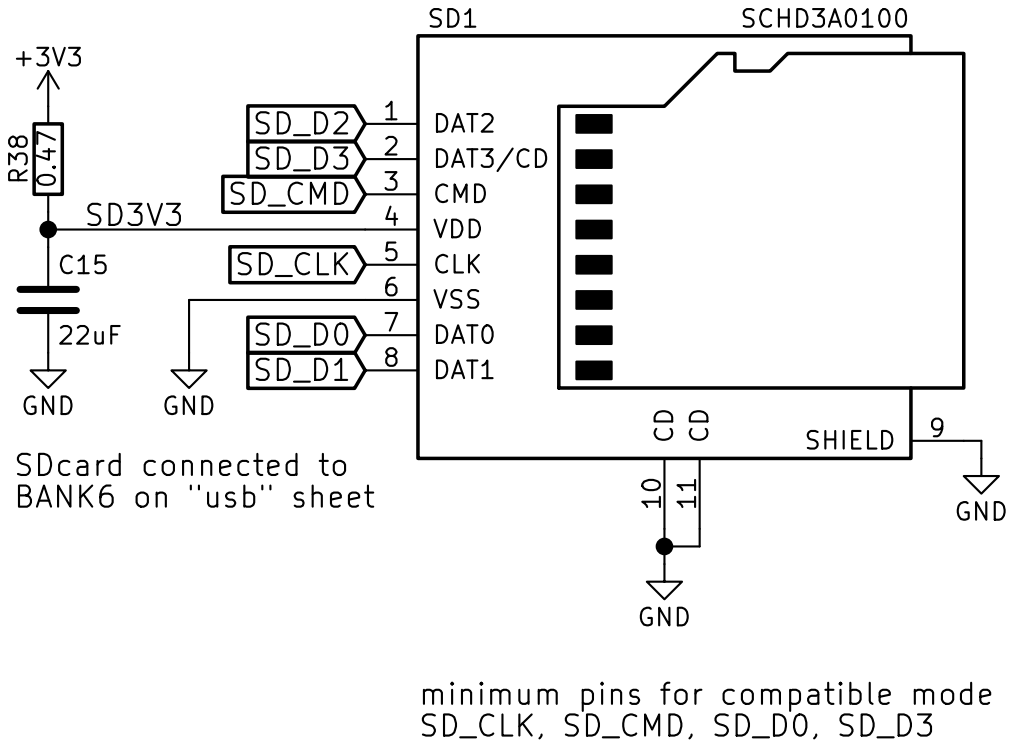
[picture p84: page 10]

minimum pins for compatible mode

File: sdcard.sch Sheet: /sdcard/ EMARD

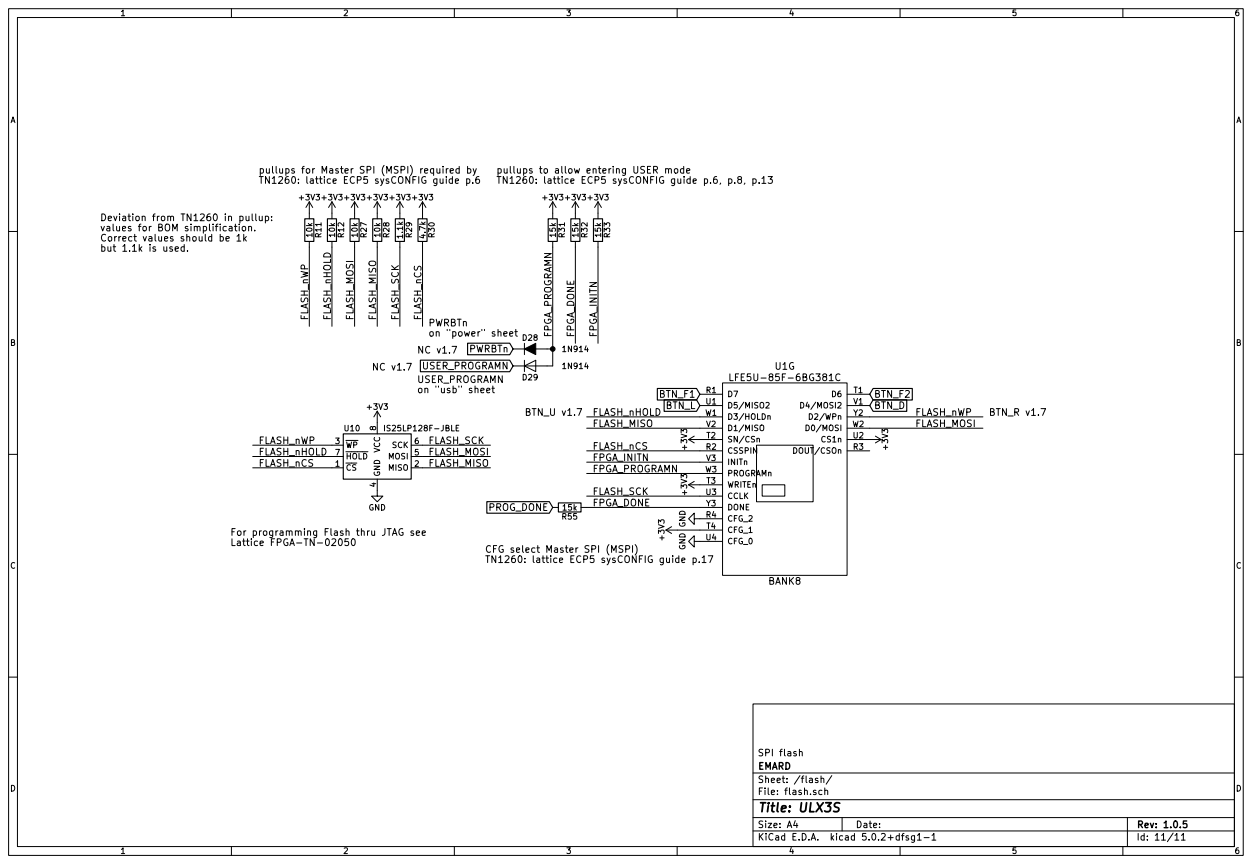
[picture p85: page 11]

+3V3 pullups for Master SPI (MSPI) required by
TN1260: lattice ECP5 sysCONFIG guide p.6 10k R11 FLASH_nWP
FPGA_DONE 15k R31 FPGA_PROGRAMN
LFE5U-85F-6BG381C

pullups to allow entering USER mode

Deviation from TN1260 in pullup:
values for BOM simplification.

on "usb" sheet PWRBTn
on "power" sheet
1N914 USER_PROGRAMN

FLASH_nHOLD | | FLASH_MOSI
FLASH_nCS | FLASH_MISO

4 MOSI 5 SCK 6 HOLD 7 VCC

For programming Flash thru JTAG see
Lattice FPGA-TN-02050

CFG select Master SPI (MSPI)
TN1260: lattice ECP5 sysCONFIG guide p.17

File: flash.sch Sheet: /flash/ EMARD
